lucsch/ESP32Marauder/esp32_marauder_pio/data/marauder3L1.jpg

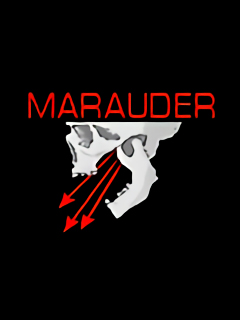
esp32_marauder_pio/data/marauder3L1.jpg
