lucsch/ESP32Marauder/esp32_marauder_pio/data/marauder_mini.jpg

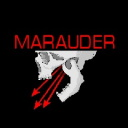
esp32_marauder_pio/data/marauder_mini.jpg
