lucsch/ESP32Marauder/pictures/jcmk_square_sticker_500px.png

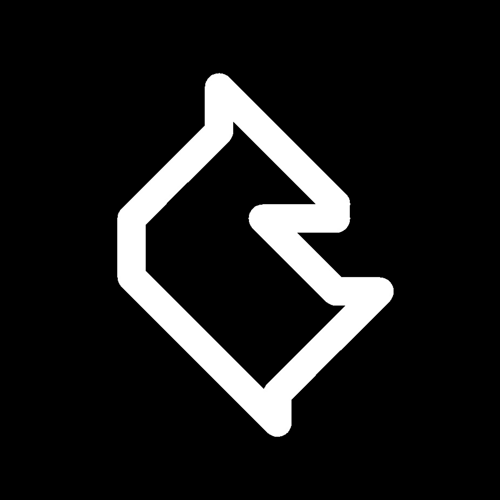
pictures/jcmk_square_sticker_500px.png
