lucsch/ESP32Marauder/mechanical/V7/Battery Cover.stl

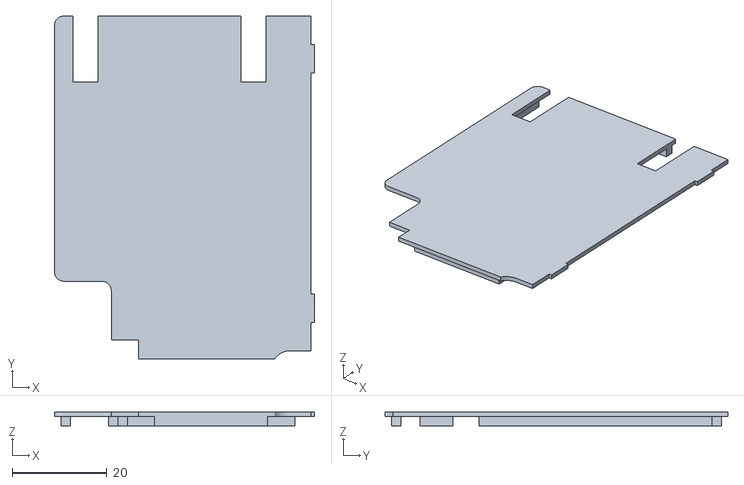
[picture p25: CAD file, 2025-01-28]
mechanical/V7/Battery Cover.stl
54.9 x 72.4 x 3.00
