lucsch/ESP32Marauder/mechanical/V7/Power Switch.stl

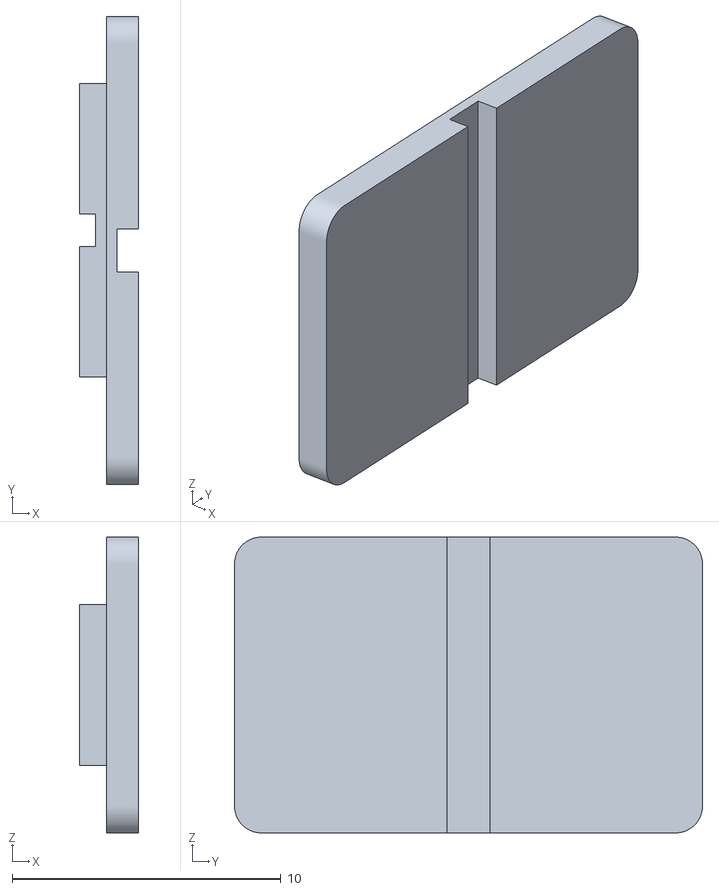
[picture p27: CAD file, 2025-01-28]
mechanical/V7/Power Switch.stl
2.20 x 17.4 x 11.0
