lucsch/ESP32Marauder/mechanical/C5 Adapter/Extra designs/c5 adapter back - hatched 1.stl

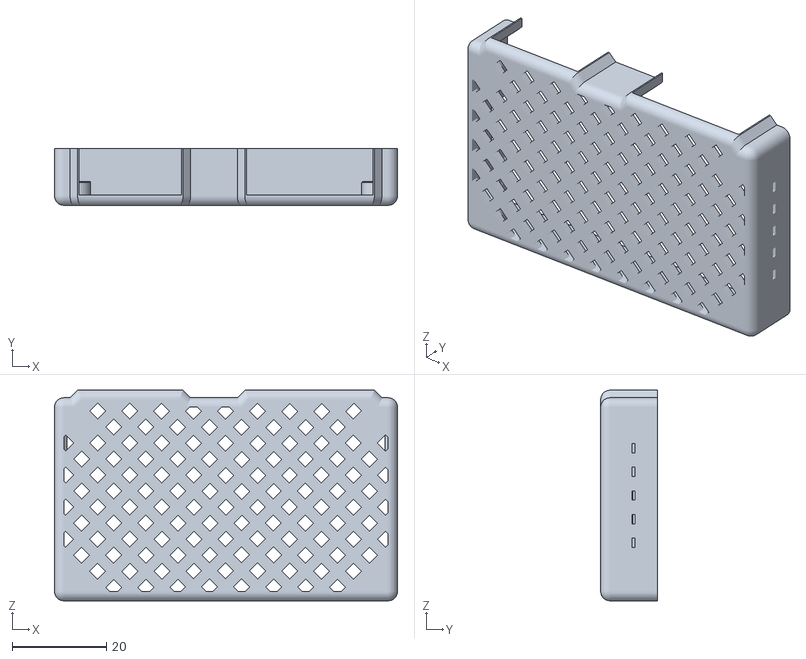
[picture p28: CAD file, 2025-09-12]
mechanical/C5 Adapter/Extra designs/c5 adapter back - hatched 1.stl
72.6 x 12.0 x 44.6
