lucsch/ESP32Marauder/pictures/BFFB NRF24 Fix/DSC05049-Edit.jpg

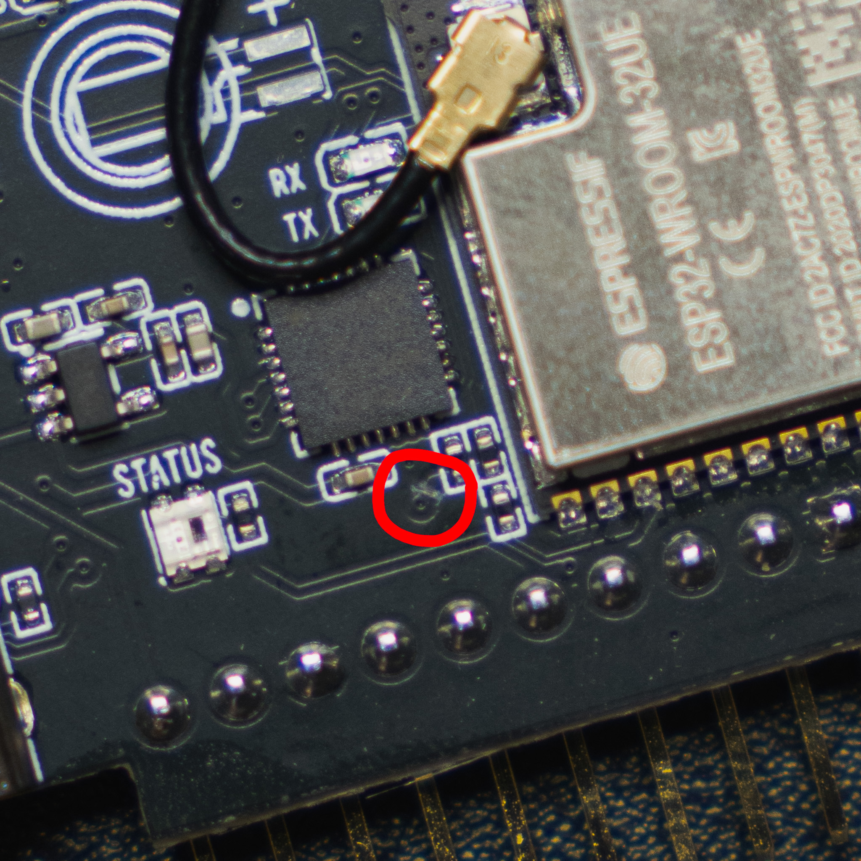
pictures/BFFB NRF24 Fix/DSC05049-Edit.jpg
