lucsch/ESP32Marauder/pictures/BFFB NRF24 Fix/DSC05050.jpg

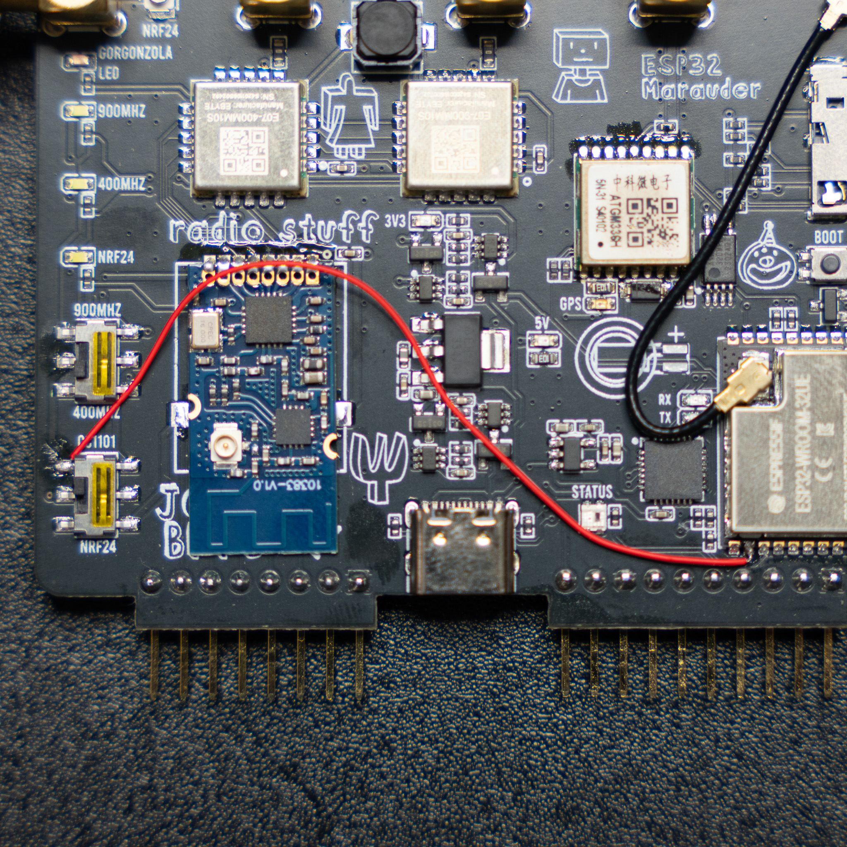
pictures/BFFB NRF24 Fix/DSC05050.jpg
