lucsch/ESP32Marauder/schematics/ch340/ch340_test.kicad_sch

## KiCad design schematics/ch340/ch340_test.kicad_sch (2024-10-28)

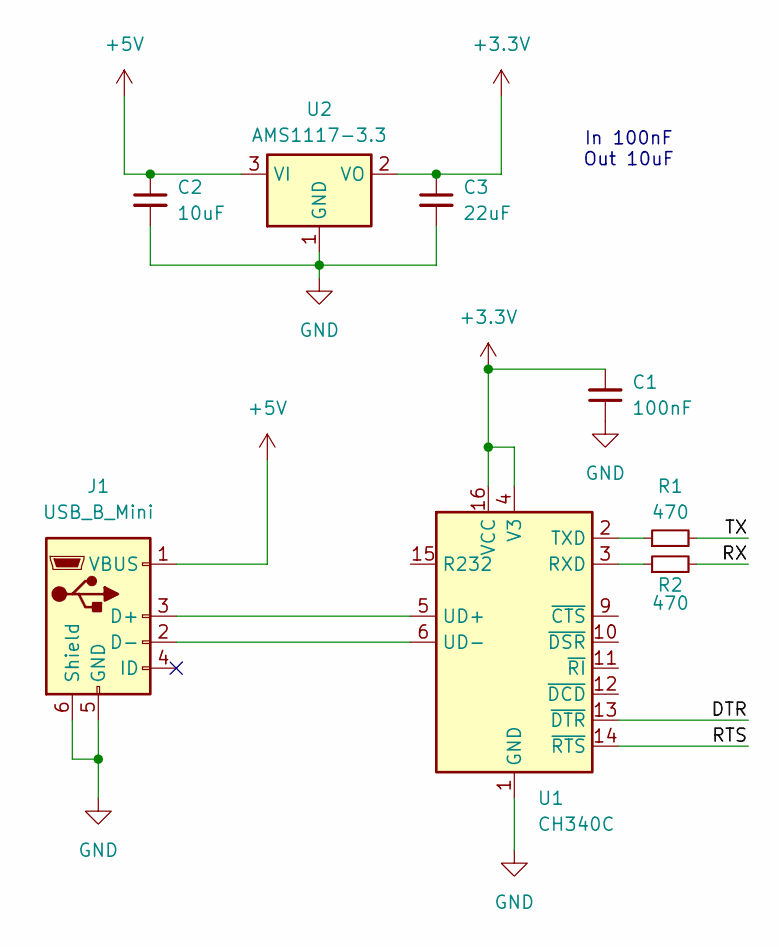
[picture p31: schematic ch340_test.kicad_sch]

Parts:
C1: 100nF
C2: 10uF
C3: 22uF
J1: USB_B_Mini
R1, R2: 470
U1: CH340C; SOIC-16_3.9x9.9mm_P1.27mm
U2: AMS1117-3.3; SOT-223-3_TabPin2

Connections:
+3.3V: C1.2, C3.1, U1.4 (V3), U1.16 (VCC), U2.2 (VO)
+5V: C2.1, J1.1 (VBUS), U2.3 (VI)
DTR: U1.13 (~DTR)
GND: C1.1, C2.2, C3.2, J1.5 (GND), J1.6 (Shield), U1.1 (GND), U2.1 (GND)
unnamed: J1.2 (D-), U1.6 (UD-)
unnamed: J1.3 (D+), U1.5 (UD+)
unnamed: R1.1, U1.2 (TXD)
unnamed: R2.1, U1.3 (RXD)
RTS: U1.14 (~RTS)
RX: R2.2
TX: R1.2

Notes on the sheet:
In 100nF Out 10uF
