lucsch/ESP32Marauder/esp32_marauder/MenuFunctions.cpp

#include "MenuFunctions.h"
#include "lang_var.h"
//#include "icons.h"

#ifdef HAS_SCREEN

extern const unsigned char menu_icons[][66];
PROGMEM lv_obj_t * slider_label;
PROGMEM lv_obj_t * ta1;
PROGMEM lv_obj_t * ta2;
PROGMEM lv_obj_t * save_name;

MenuFunctions::MenuFunctions()
{
}

// LVGL Stuff
/* Interrupt driven periodic handler */

#ifdef HAS_ILI9341
  void MenuFunctions::lv_tick_handler()
  {
    lv_tick_inc(LVGL_TICK_PERIOD);
  }
  
  /* Display flushing */
  void my_disp_flush(lv_disp_drv_t *disp, const lv_area_t *area, lv_color_t *color_p)
  {
    extern Display display_obj;
    uint16_t c;
  
    display_obj.tft.startWrite();
    display_obj.tft.setAddrWindow(area->x1, area->y1, (area->x2 - area->x1 + 1), (area->y2 - area->y1 + 1));
    for (int y = area->y1; y <= area->y2; y++) {
      for (int x = area->x1; x <= area->x2; x++) {
        c = color_p->full;
        display_obj.tft.writeColor(c, 1);
        color_p++;
      }
    }
    display_obj.tft.endWrite();
    lv_disp_flush_ready(disp);
  }
  
  
  bool my_touchpad_read(lv_indev_drv_t * indev_driver, lv_indev_data_t * data)
  {
    extern Display display_obj;
    
    uint16_t touchX, touchY;
  
    bool touched = display_obj.updateTouch(&touchX, &touchY, 600);
  
    if(!touched)
    {
      return false;
    }
  
    if(touchX>WIDTH_1 || touchY > HEIGHT_1)
    {
      Serial.println("Y or y outside of expected parameters..");
      Serial.print("y:");
      Serial.print(touchX);
      Serial.print(" x:");
      Serial.print(touchY);
    }
    else
    {
  
      data->state = touched ? LV_INDEV_STATE_PR : LV_INDEV_STATE_REL; 
       
      data->point.x = touchX;
      data->point.y = touchY;
  
    }
  
    return false;
  }
  
  void MenuFunctions::initLVGL() {
    tick.attach_ms(LVGL_TICK_PERIOD, lv_tick_handler);
    
    lv_init();
  
    lv_disp_buf_init(&disp_buf, buf, NULL, LV_HOR_RES_MAX * 10);
  
    lv_disp_drv_t disp_drv;
    lv_disp_drv_init(&disp_drv);
    disp_drv.hor_res = WIDTH_1;
    disp_drv.ver_res = HEIGHT_1;
    disp_drv.flush_cb = my_disp_flush;
    disp_drv.buffer = &disp_buf;
    lv_disp_drv_register(&disp_drv);
  
    lv_indev_drv_t indev_drv;
    lv_indev_drv_init(&indev_drv);             
    indev_drv.type = LV_INDEV_TYPE_POINTER;    
    indev_drv.read_cb = my_touchpad_read;      
    lv_indev_drv_register(&indev_drv);         
  }
  
  
  void MenuFunctions::deinitLVGL() {
    Serial.println(F("Deinit LVGL"));
    //lv_deinit();
  }
  
  
  // Event handler for settings drop down menus
  void setting_dropdown_cb(lv_obj_t * obj, lv_event_t event) {

  }

  // GFX Function to build a list showing all Stations scanned
  void MenuFunctions::addStationGFX(){
    extern LinkedList<Station>* stations;
    extern LinkedList<AccessPoint>* access_points;
    extern WiFiScan wifi_scan_obj;
  
    lv_obj_t * list1 = lv_list_create(lv_scr_act(), NULL);
    lv_obj_set_size(list1, 160, 200);
    lv_obj_set_width(list1, LV_HOR_RES);
    lv_obj_align(list1, NULL, LV_ALIGN_CENTER, 0, 0);
  
    lv_obj_t * list_btn;
  
    lv_obj_t * label;
  
    list_btn = lv_list_add_btn(list1, LV_SYMBOL_CLOSE, text09);
    lv_obj_set_event_cb(list_btn, station_list_cb);

    char addr[] = "00:00:00:00:00:00";
    for (int x = 0; x < access_points->size(); x++) {
      AccessPoint cur_ap = access_points->get(x);

      // Add non clickable button for AP
      String full_label = "AP: " + cur_ap.essid;
      char buf[full_label.length() + 1] = {};
      full_label.toCharArray(buf, full_label.length() + 1);
      list_btn = lv_list_add_btn(list1, NULL, buf);
      lv_btn_set_checkable(list_btn, false);
      
      int cur_ap_sta_len = access_points->get(x).stations->size();
      for (int y = 0; y < cur_ap_sta_len; y++) {
        Station cur_sta = stations->get(cur_ap.stations->get(y));
        // Convert uint8_t MAC to char array
        wifi_scan_obj.getMAC(addr, cur_sta.mac, 0);
        
        list_btn = lv_list_add_btn(list1, LV_SYMBOL_WIFI, addr);
        lv_btn_set_checkable(list_btn, true);
        lv_obj_set_event_cb(list_btn, station_list_cb);
    
        if (cur_sta.selected)
          lv_btn_toggle(list_btn);
      }
    }
  }

  // Function to work with list of Stations
  void station_list_cb(lv_obj_t * btn, lv_event_t event) {
    extern LinkedList<Station>* stations;
    extern MenuFunctions menu_function_obj;
    extern WiFiScan wifi_scan_obj;
  
    String btn_text = lv_list_get_btn_text(btn);
    String display_string = "";
    char addr[] = "00:00:00:00:00:00";
    
    if (event == LV_EVENT_CLICKED) {
      if (btn_text != text09) {
      }
      else {
        Serial.println("Exiting...");
        lv_obj_del_async(lv_obj_get_parent(lv_obj_get_parent(btn)));
  
        for (int i = 0; i < stations->size(); i++) {
          if (stations->get(i).selected) {
            wifi_scan_obj.getMAC(addr, stations->get(i).mac, 0);
            Serial.print("Selected: ");
            Serial.println(addr);
          }
        }
  
        printf("LV_EVENT_CANCEL\n");
        menu_function_obj.deinitLVGL();
        wifi_scan_obj.StartScan(WIFI_SCAN_OFF);
        display_obj.exit_draw = true; // set everything back to normal
      }
    }
    
    if (event == LV_EVENT_VALUE_CHANGED) {     
      if (lv_btn_get_state(btn) == LV_BTN_STATE_CHECKED_RELEASED) {
        for (int i = 0; i < stations->size(); i++) {
          wifi_scan_obj.getMAC(addr, stations->get(i).mac, 0); 
          if (strcmp(addr, btn_text.c_str()) == 0) {
            Serial.print("Adding Station: ");
            Serial.println(addr);
            Station sta = stations->get(i);
            sta.selected = true;
            stations->set(i, sta);
          }
        }
      }
      else {
        for (int i = 0; i < stations->size(); i++) {
          wifi_scan_obj.getMAC(addr, stations->get(i).mac, 0); 
          if (strcmp(addr, btn_text.c_str()) == 0) {
            Serial.print("Removing Station: ");
            Serial.println(addr);
            Station sta = stations->get(i);
            sta.selected = false;
            stations->set(i, sta);
          }
        }
      }
    }
  }

  // GFX Function to build a list showing all EP HTML Files
  void MenuFunctions::selectEPHTMLGFX() {
    extern EvilPortal evil_portal_obj;
  
    lv_obj_t * list1 = lv_list_create(lv_scr_act(), NULL);
    lv_obj_set_size(list1, 160, 200);
    lv_obj_set_width(list1, LV_HOR_RES);
    lv_obj_align(list1, NULL, LV_ALIGN_CENTER, 0, 0);
  
    lv_obj_t * list_btn;
  
    lv_obj_t * label;
  
    list_btn = lv_list_add_btn(list1, LV_SYMBOL_CLOSE, text09);
    lv_obj_set_event_cb(list_btn, html_list_cb);
  
    for (int i = 1; i < evil_portal_obj.html_files->size(); i++) {
      char buf[evil_portal_obj.html_files->get(i).length() + 1] = {};
      evil_portal_obj.html_files->get(i).toCharArray(buf, evil_portal_obj.html_files->get(i).length() + 1);
      
      list_btn = lv_list_add_btn(list1, LV_SYMBOL_FILE, buf);
      lv_btn_set_checkable(list_btn, true);
      lv_obj_set_event_cb(list_btn, html_list_cb);
  
      if (i == evil_portal_obj.selected_html_index)
        lv_btn_toggle(list_btn);
    }
  }

  void html_list_cb(lv_obj_t * btn, lv_event_t event) {
    extern EvilPortal evil_portal_obj;
    extern MenuFunctions menu_function_obj;
  
    String btn_text = lv_list_get_btn_text(btn);
    String display_string = "";
    
    if (event == LV_EVENT_CLICKED) {
      if (btn_text != text09) {
      }
      else {
        Serial.println("Exiting...");
        lv_obj_del_async(lv_obj_get_parent(lv_obj_get_parent(btn)));
  
        for (int i = 1; i < evil_portal_obj.html_files->size(); i++) {
          if (i == evil_portal_obj.selected_html_index) {
            Serial.println("Selected: " + (String)evil_portal_obj.html_files->get(i));
          }
        }
  
        printf("LV_EVENT_CANCEL\n");
        menu_function_obj.deinitLVGL();
        wifi_scan_obj.StartScan(WIFI_SCAN_OFF);
        display_obj.exit_draw = true; // set everything back to normal
      }
    }
    
    if (event == LV_EVENT_VALUE_CHANGED) {      
      if (lv_btn_get_state(btn) == LV_BTN_STATE_CHECKED_RELEASED) {
        for (int i = 1; i < evil_portal_obj.html_files->size(); i++) {
          if (evil_portal_obj.html_files->get(i) == btn_text) {
            Serial.println("Setting HTML: " + (String)evil_portal_obj.html_files->get(i));
            evil_portal_obj.selected_html_index = i;
            evil_portal_obj.target_html_name = (String)evil_portal_obj.html_files->get(i);
          }
        }

        // Deselect buttons that were previously selected
        lv_obj_t * list = lv_obj_get_parent(btn);

        lv_obj_t * next_btn = lv_obj_get_child(list, NULL);
        while (next_btn != NULL) {
          if (next_btn != btn) {
            lv_btn_set_state(next_btn, LV_BTN_STATE_RELEASED);
          }
          next_btn = lv_obj_get_child(list, next_btn);
        }
      }
    }
  }
  
  // GFX Function to build a list showing all APs scanned
  void MenuFunctions::addAPGFX(String type){
    extern WiFiScan wifi_scan_obj;
    extern LinkedList<AccessPoint>* access_points;
    extern LinkedList<AirTag>* airtags;
  
    lv_obj_t * list1 = lv_list_create(lv_scr_act(), NULL);
    lv_obj_set_size(list1, 160, 200);
    lv_obj_set_width(list1, LV_HOR_RES);
    lv_obj_align(list1, NULL, LV_ALIGN_CENTER, 0, 0);
  
    lv_obj_t * list_btn;
  
    lv_obj_t * label;
  
    list_btn = lv_list_add_btn(list1, LV_SYMBOL_CLOSE, text09);
    lv_obj_set_event_cb(list_btn, ap_list_cb);
  
    if ((type == "AP") || (type == "AP Info")) {
      for (int i = 0; i < access_points->size(); i++) {
        char buf[access_points->get(i).essid.length() + 1] = {};
        access_points->get(i).essid.toCharArray(buf, access_points->get(i).essid.length() + 1);
        
        list_btn = lv_list_add_btn(list1, LV_SYMBOL_WIFI, buf);
        lv_btn_set_checkable(list_btn, true);
        if (type == "AP")
          lv_obj_set_event_cb(list_btn, ap_list_cb);
        else if (type == "AP Info")
          lv_obj_set_event_cb(list_btn, ap_info_list_cb);
    
        if (access_points->get(i).selected)
          lv_btn_toggle(list_btn);
      }
    }
    else if (type == "Airtag") {
      for (int i = 0; i < airtags->size(); i++) {
        char buf[airtags->get(i).mac.length() + 1] = {};
        airtags->get(i).mac.toCharArray(buf, airtags->get(i).mac.length() + 1);
        
        list_btn = lv_list_add_btn(list1, LV_SYMBOL_BLUETOOTH, buf);
        lv_btn_set_checkable(list_btn, true);
        lv_obj_set_event_cb(list_btn, at_list_cb);
    
        //if (airtags->get(i).selected)
        //  lv_btn_toggle(list_btn);
      }
    }
  }
  
  void at_list_cb(lv_obj_t * btn, lv_event_t event) {
    extern MenuFunctions menu_function_obj;
    extern WiFiScan wifi_scan_obj;
    extern LinkedList<AirTag>* airtags;
    extern Display display_obj;
  
    String btn_text = lv_list_get_btn_text(btn);
    String display_string = "";
    
    // Button is clicked
    if (event == LV_EVENT_CLICKED) {
      if (btn_text != text09) {
      }
      // It's the back button
      else {
        Serial.println("Exiting...");
        lv_obj_del_async(lv_obj_get_parent(lv_obj_get_parent(btn)));
  
        for (int i = 0; i < airtags->size(); i++) {
          if (airtags->get(i).selected) {
            Serial.println("Selected: " + (String)airtags->get(i).mac);
          }
        }
  
        printf("LV_EVENT_CANCEL\n");
        menu_function_obj.deinitLVGL();
        wifi_scan_obj.StartScan(WIFI_SCAN_OFF);
        display_obj.exit_draw = true; // set everything back to normal
      }
    }
    
    if (event == LV_EVENT_VALUE_CHANGED) {      
      if (lv_btn_get_state(btn) == LV_BTN_STATE_CHECKED_RELEASED) {
        bool do_that_thang = false;
        for (int i = 0; i < airtags->size(); i++) {
          if (airtags->get(i).mac == btn_text) {
            Serial.println("Selecting Airtag: " + (String)airtags->get(i).mac);
            AirTag at = airtags->get(i);
            at.selected = true;
            airtags->set(i, at);
            do_that_thang = true;
          }
          else {
            AirTag at = airtags->get(i);
            at.selected = false;
            airtags->set(i, at);
          }
        }
        // Start spoofing airtag
        if (do_that_thang) {
          menu_function_obj.deinitLVGL();
          lv_obj_del_async(lv_obj_get_parent(lv_obj_get_parent(btn)));
          wifi_scan_obj.StartScan(WIFI_SCAN_OFF);
          display_obj.clearScreen();
          menu_function_obj.orientDisplay();
          display_obj.clearScreen();
          menu_function_obj.drawStatusBar();
          wifi_scan_obj.StartScan(BT_SPOOF_AIRTAG, TFT_WHITE);
        }
      }
      else {
        for (int i = 0; i < airtags->size(); i++) {
          if (airtags->get(i).mac == btn_text) {
            Serial.println("Deselecting Airtag: " + (String)airtags->get(i).mac);
            AirTag at = airtags->get(i);
            at.selected = false;
            airtags->set(i, at);
          }
        }
      }
    }
  }
  
  void ap_list_cb(lv_obj_t * btn, lv_event_t event) {
    extern LinkedList<AccessPoint>* access_points;
    extern MenuFunctions menu_function_obj;
    extern WiFiScan wifi_scan_obj;
  
    String btn_text = lv_list_get_btn_text(btn);
    String display_string = "";
    
    if (event == LV_EVENT_CLICKED) {
      if (btn_text != text09) {
      }
      else {
        Serial.println("Exiting...");
        lv_obj_del_async(lv_obj_get_parent(lv_obj_get_parent(btn)));
  
        for (int i = 0; i < access_points->size(); i++) {
          if (access_points->get(i).selected) {
            Serial.println("Selected: " + (String)access_points->get(i).essid);
          }
        }
  
        printf("LV_EVENT_CANCEL\n");
        menu_function_obj.deinitLVGL();
        wifi_scan_obj.StartScan(WIFI_SCAN_OFF);
        display_obj.exit_draw = true; // set everything back to normal
      }
    }
    
    if (event == LV_EVENT_VALUE_CHANGED) {      
      if (lv_btn_get_state(btn) == LV_BTN_STATE_CHECKED_RELEASED) {
        for (int i = 0; i < access_points->size(); i++) {
          if (access_points->get(i).essid == btn_text) {
            Serial.println("Adding AP: " + (String)access_points->get(i).essid);
            AccessPoint ap = access_points->get(i);
            ap.selected = true;
            access_points->set(i, ap);
          }
        }
      }
      else {
        for (int i = 0; i < access_points->size(); i++) {
          if (access_points->get(i).essid == btn_text) {
            Serial.println("Removing AP: " + (String)access_points->get(i).essid);
            AccessPoint ap = access_points->get(i);
            ap.selected = false;
            access_points->set(i, ap);
          }
        }
      }
    }
  }

  void ap_info_list_cb(lv_obj_t * btn, lv_event_t event) {
    extern LinkedList<AccessPoint>* access_points;
    extern MenuFunctions menu_function_obj;
    extern WiFiScan wifi_scan_obj;
  
    String btn_text = lv_list_get_btn_text(btn);
    String display_string = "";
    
    // Exit function
    if (event == LV_EVENT_CLICKED) {
      if (btn_text != text09) {
        for (int i = 0; i < access_points->size(); i++) {
          if (access_points->get(i).essid == btn_text) {
            lv_obj_del_async(lv_obj_get_parent(lv_obj_get_parent(btn)));
  
            printf("LV_EVENT_CANCEL\n");
            menu_function_obj.deinitLVGL();
            wifi_scan_obj.StartScan(WIFI_SCAN_OFF);
            //display_obj.exit_draw = true; // set everything back to normal
            menu_function_obj.orientDisplay();
            menu_function_obj.changeMenu(&menu_function_obj.apInfoMenu);
            wifi_scan_obj.RunAPInfo(i);
          }
        }
      }
      else {
        Serial.println("Exiting...");
        lv_obj_del_async(lv_obj_get_parent(lv_obj_get_parent(btn)));
  
        printf("LV_EVENT_CANCEL\n");
        menu_function_obj.deinitLVGL();
        wifi_scan_obj.StartScan(WIFI_SCAN_OFF);
        display_obj.exit_draw = true; // set everything back to normal
      }
    }
  }
  
  void MenuFunctions::addSSIDGFX(){
    extern LinkedList<ssid>* ssids;
    
    String display_string = "";
    // Create a keyboard and apply the styles
    kb = lv_keyboard_create(lv_scr_act(), NULL);
    lv_obj_set_size(kb, LV_HOR_RES, LV_VER_RES / 2);
    lv_obj_set_event_cb(kb, add_ssid_keyboard_event_cb);
  
    // Create one text area
    // Store all SSIDs
    ta1 = lv_textarea_create(lv_scr_act(), NULL);
    lv_textarea_set_one_line(ta1, false);
    lv_obj_set_width(ta1, LV_HOR_RES);
    lv_obj_set_height(ta1, (LV_VER_RES / 2) - 35);
    lv_obj_set_pos(ta1, 5, 20);
    lv_textarea_set_cursor_hidden(ta1, true);
    lv_obj_align(ta1, NULL, LV_ALIGN_IN_TOP_MID, NULL, NULL);
    lv_textarea_set_placeholder_text(ta1, text_table1[0]);
  
    // Create second text area
    // Add SSIDs
    ta2 = lv_textarea_create(lv_scr_act(), ta1);
    lv_textarea_set_cursor_hidden(ta2, false);
    lv_textarea_set_one_line(ta2, true);
    lv_obj_align(ta2, NULL, LV_ALIGN_IN_TOP_MID, NULL, (LV_VER_RES / 2) - 35);
    lv_textarea_set_text(ta2, "");
    lv_textarea_set_placeholder_text(ta2, text_table1[1]);
  
    // After generating text areas, add text to first text box
    for (int i = 0; i < ssids->size(); i++)
      display_string.concat((String)ssids->get(i).essid + "\n");
      
    lv_textarea_set_text(ta1, display_string.c_str());
  
    // Focus it on one of the text areas to start
    lv_keyboard_set_textarea(kb, ta2);
    lv_keyboard_set_cursor_manage(kb, true);
    
  }
  
  // Keyboard callback dedicated to joining wifi
  void add_ssid_keyboard_event_cb(lv_obj_t * keyboard, lv_event_t event){
    extern Display display_obj;
    extern MenuFunctions menu_function_obj;
    extern WiFiScan wifi_scan_obj;
    extern LinkedList<ssid>* ssids;
    
    lv_keyboard_def_event_cb(kb, event);
  
    // User has applied text box
    if(event == LV_EVENT_APPLY){
      String display_string = "";
      printf("LV_EVENT_APPLY\n");
  
      // Get text from SSID text box
      String ta2_text = lv_textarea_get_text(ta2);
      Serial.println(ta2_text);
  
      // Add text box text to list of SSIDs
      wifi_scan_obj.addSSID(ta2_text);
  
      // Update large text box with ssid
      for (int i = 0; i < ssids->size(); i++)
        display_string.concat((String)ssids->get(i).essid + "\n");
      lv_textarea_set_text(ta1, display_string.c_str());
  
      lv_textarea_set_text(ta2, "");
    }else if(event == LV_EVENT_CANCEL){
      printf("LV_EVENT_CANCEL\n");
      menu_function_obj.deinitLVGL();
      display_obj.exit_draw = true; // set everything back to normal
    }
  }

  void MenuFunctions::joinWiFiGFX(String essid){

    // Create one text area
    ta1 = lv_textarea_create(lv_scr_act(), NULL);
    lv_textarea_set_one_line(ta1, true);
    lv_obj_set_width(ta1, LV_HOR_RES / 2 - 20);
    lv_obj_set_pos(ta1, 5, 20);
    //lv_ta_set_cursor_type(ta, LV_CURSOR_BLOCK);
    lv_textarea_set_text(ta1, essid.c_str());
    lv_obj_set_event_cb(ta1, ta_event_cb);

    // Create first label
    lv_obj_t * ssid_label = lv_label_create(lv_scr_act(), NULL);
    lv_label_set_text(ssid_label, "SSID:");
    lv_obj_align(ssid_label, ta1, LV_ALIGN_OUT_TOP_LEFT, 0, 0);

    // Create second text area
    ta2 = lv_textarea_create(lv_scr_act(), ta1);
    //lv_textarea_set_pwd_mode(ta2, true); // This shit makes it so backspace does not work
    //lv_textarea_set_pwd_show_time(ta2, 1000);
    lv_textarea_set_cursor_hidden(ta2, true);
    lv_obj_align(ta2, NULL, LV_ALIGN_IN_TOP_RIGHT, -5, 20);

    // Create second label
    lv_obj_t * pw_label = lv_label_create(lv_scr_act(), NULL);
    lv_label_set_text(pw_label, "Password:");
    lv_textarea_set_text(ta2, "");
    lv_obj_align(pw_label, ta2, LV_ALIGN_OUT_TOP_LEFT, 0, 0);

    // Create a keyboard and apply the styles
    kb = lv_keyboard_create(lv_scr_act(), NULL);
    lv_obj_set_size(kb, LV_HOR_RES, LV_VER_RES / 2);
    lv_obj_set_event_cb(kb, join_wifi_keyboard_event_cb);

    // Focus it on one of the text areas to start
    lv_keyboard_set_textarea(kb, ta1);
    lv_keyboard_set_cursor_manage(kb, true);
    
  }

  void join_wifi_keyboard_event_cb(lv_obj_t * keyboard, lv_event_t event){
    extern Display display_obj;
    extern MenuFunctions menu_function_obj;
    extern WiFiScan wifi_scan_obj;
    lv_keyboard_def_event_cb(kb, event);
    if(event == LV_EVENT_APPLY){
      printf("LV_EVENT_APPLY\n");
      //String ta1_text = lv_textarea_get_text(lv_keyboard_get_textarea(kb));
      String ta1_text = lv_textarea_get_text(ta1);
      String ta2_text = lv_textarea_get_text(ta2);
      Serial.println(ta1_text);
      Serial.println(ta2_text);
      if (wifi_scan_obj.joinWiFi(ta1_text, ta2_text))
        wifi_scan_obj.currentScanMode = WIFI_CONNECTED;
      else
        wifi_scan_obj.currentScanMode = WIFI_SCAN_OFF;
    }else if(event == LV_EVENT_CANCEL){
      printf("LV_EVENT_CANCEL\n");
      //lv_textarea_set_text(lv_keyboard_get_textarea(kb), "");
      menu_function_obj.deinitLVGL();
      //wifi_scan_obj.StartScan(WIFI_SCAN_OFF);
      display_obj.exit_draw = true; // set everything back to normal
      if (wifi_scan_obj.connected_network != "")
        wifi_scan_obj.currentScanMode = WIFI_CONNECTED;
    }
  }
  
  
  void ta_event_cb(lv_obj_t * ta, lv_event_t event)
  {
    if(event == LV_EVENT_CLICKED) {
      if(kb != NULL)
        lv_keyboard_set_textarea(kb, ta);
    }
  
  }

#endif
//// END LV_ARDUINO STUFF

void MenuFunctions::buttonNotSelected(int b, int x) {
  if (x == -1)
    x = b;

  // Ensure b is within valid button index range
  b = (x - menu_start_index) % BUTTON_SCREEN_LIMIT;

  #ifdef HAS_MINI_SCREEN
    display_obj.tft.setFreeFont(NULL);
    display_obj.key[b].drawButton(false, current_menu->list->get(x).name);
  #endif

  uint16_t color = this->getColor(current_menu->list->get(x).color);

  #ifdef HAS_FULL_SCREEN
    display_obj.tft.setFreeFont(MENU_FONT);
    display_obj.key[b].drawButton(false, current_menu->list->get(x).name);
    if ((current_menu->list->get(x).name != text09) && (current_menu->list->get(x).icon != 255))
          display_obj.tft.drawXBitmap(0,
                                      KEY_Y + (b * (KEY_H + KEY_SPACING_Y)) - (ICON_H / 2),
                                      menu_icons[current_menu->list->get(x).icon],
                                      ICON_W,
                                      ICON_H,
                                      TFT_BLACK,
                                      color);
    display_obj.tft.setFreeFont(NULL);
  #endif
}

void MenuFunctions::buttonSelected(int b, int x) {
  if (x == -1)
    x = b;

  // Ensure b is within valid button index range
  b = (x - menu_start_index) % BUTTON_SCREEN_LIMIT;

  uint16_t color = this->getColor(current_menu->list->get(x).color);

  #ifdef HAS_MINI_SCREEN
    display_obj.tft.setFreeFont(NULL);
    display_obj.key[b].drawButton(true, current_menu->list->get(x).name);
  #endif

  #ifdef HAS_FULL_SCREEN
    display_obj.tft.setFreeFont(MENU_FONT);
    display_obj.key[b].drawButton(true, current_menu->list->get(x).name);
    if ((current_menu->list->get(x).name != text09) && (current_menu->list->get(x).icon != 255))
          display_obj.tft.drawXBitmap(0,
                                      KEY_Y + (b * (KEY_H + KEY_SPACING_Y)) - (ICON_H / 2),
                                      menu_icons[current_menu->list->get(x).icon],
                                      ICON_W,
                                      ICON_H,
                                      TFT_BLACK,
                                      color);
    display_obj.tft.setFreeFont(NULL);
  #endif
}

void MenuFunctions::displayMenuButtons() {
  #ifdef HAS_ILI9341
    // Draw lines to show each menu button
    for (int i = 0; i < 3; i++) {

      // Draw horizontal line on left
      display_obj.tft.drawLine(0, 
                              TFT_HEIGHT / 3 * (i),
                              (TFT_WIDTH / 12) / 2,
                              TFT_HEIGHT / 3 * (i),
                              TFT_FARTGRAY);

      // Draw horizontal line on right
      display_obj.tft.drawLine(TFT_WIDTH - 1 - ((TFT_WIDTH / 12) / 2), 
                              TFT_HEIGHT / 3 * (i),
                              TFT_WIDTH,
                              TFT_HEIGHT / 3 * (i),
                              TFT_FARTGRAY);

      // Draw vertical line on left
      display_obj.tft.drawLine(0, 
                              (TFT_HEIGHT / 3 * (i)) - ((TFT_WIDTH / 12) / 2),
                              0,
                              (TFT_HEIGHT / 3 * (i)) + ((TFT_WIDTH / 12) / 2),
                              TFT_FARTGRAY);

      // Draw vertical line on right
      display_obj.tft.drawLine(TFT_WIDTH - 1, 
                              (TFT_HEIGHT / 3 * (i)) - ((TFT_WIDTH / 12) / 2),
                              TFT_WIDTH - 1,
                              (TFT_HEIGHT / 3 * (i)) + ((TFT_WIDTH / 12) / 2),
                              TFT_FARTGRAY);
    }
  #endif
}

// Function to check menu input
void MenuFunctions::main(uint32_t currentTime)
{
  // Some function exited and we need to go back to normal
  if (display_obj.exit_draw) {
    if (wifi_scan_obj.currentScanMode != WIFI_CONNECTED)
      wifi_scan_obj.currentScanMode = WIFI_SCAN_OFF;
    display_obj.exit_draw = false;
    this->orientDisplay();
  }
  if ((wifi_scan_obj.currentScanMode == WIFI_SCAN_OFF) ||
      (wifi_scan_obj.currentScanMode == WIFI_CONNECTED) ||
      (wifi_scan_obj.currentScanMode == OTA_UPDATE) ||
      (wifi_scan_obj.currentScanMode == ESP_UPDATE) ||
      (wifi_scan_obj.currentScanMode == SHOW_INFO) ||
      (wifi_scan_obj.currentScanMode == WIFI_SCAN_GPS_DATA) ||
      (wifi_scan_obj.currentScanMode == GPS_POI) ||
      (wifi_scan_obj.currentScanMode == GPS_TRACKER) ||
      (wifi_scan_obj.currentScanMode == WIFI_SCAN_GPS_NMEA)) {
    if (wifi_scan_obj.orient_display) {
      this->orientDisplay();
      wifi_scan_obj.orient_display = false;
    }
  }

  if (currentTime != 0) {
    if (currentTime - initTime >= BANNER_TIME) {
      this->initTime = millis();
      if ((wifi_scan_obj.currentScanMode != LV_JOIN_WIFI) &&
          (wifi_scan_obj.currentScanMode != LV_ADD_SSID))
        this->updateStatusBar();
      
      // Do channel analyzer stuff
      if ((wifi_scan_obj.currentScanMode == WIFI_SCAN_CHAN_ANALYZER) ||
          (wifi_scan_obj.currentScanMode == BT_SCAN_ANALYZER)){
        #ifdef HAS_SCREEN
          this->setGraphScale(this->graphScaleCheck(wifi_scan_obj._analyzer_values));

          this->drawGraph(wifi_scan_obj._analyzer_values);
        #endif
      }
    }
  }


  boolean pressed = false;
  // This is code from bodmer's keypad example
  uint16_t t_x = 0, t_y = 0; // To store the touch coordinates

  // Get the display buffer out of the way
  if ((wifi_scan_obj.currentScanMode != WIFI_SCAN_OFF ) &&
      (wifi_scan_obj.currentScanMode != WIFI_CONNECTED) &&
      (wifi_scan_obj.currentScanMode != WIFI_ATTACK_BEACON_SPAM) &&
      (wifi_scan_obj.currentScanMode != WIFI_ATTACK_AP_SPAM) &&
      (wifi_scan_obj.currentScanMode != WIFI_ATTACK_AUTH) &&
      (wifi_scan_obj.currentScanMode != WIFI_ATTACK_DEAUTH) &&
      (wifi_scan_obj.currentScanMode != WIFI_ATTACK_DEAUTH_MANUAL) &&
      (wifi_scan_obj.currentScanMode != WIFI_ATTACK_DEAUTH_TARGETED) &&
      (wifi_scan_obj.currentScanMode != WIFI_ATTACK_BAD_MSG_TARGETED) &&
      (wifi_scan_obj.currentScanMode != WIFI_ATTACK_BAD_MSG) &&
      (wifi_scan_obj.currentScanMode != WIFI_ATTACK_SLEEP) &&
      (wifi_scan_obj.currentScanMode != WIFI_ATTACK_SLEEP_TARGETED) &&
      (wifi_scan_obj.currentScanMode != WIFI_ATTACK_MIMIC) &&
      (wifi_scan_obj.currentScanMode != WIFI_ATTACK_RICK_ROLL))
    display_obj.displayBuffer();


  int pre_getTouch = millis();

  #ifdef HAS_ILI9341
    if (!this->disable_touch)
      pressed = display_obj.updateTouch(&t_x, &t_y);
  #endif


  // This is if there are scans/attacks going on
  #ifdef HAS_ILI9341
    if ((wifi_scan_obj.currentScanMode != WIFI_SCAN_OFF) &&
        (pressed) &&
        (wifi_scan_obj.currentScanMode != WIFI_CONNECTED) &&
        (wifi_scan_obj.currentScanMode != OTA_UPDATE) &&
        (wifi_scan_obj.currentScanMode != ESP_UPDATE) &&
        (wifi_scan_obj.currentScanMode != SHOW_INFO) &&
        (wifi_scan_obj.currentScanMode != WIFI_SCAN_GPS_DATA) &&
        (wifi_scan_obj.currentScanMode != GPS_POI) &&
        (wifi_scan_obj.currentScanMode != GPS_TRACKER) &&
        (wifi_scan_obj.currentScanMode != WIFI_SCAN_GPS_NMEA))
    {
      // Stop the current scan
      if ((wifi_scan_obj.currentScanMode == WIFI_SCAN_PROBE) ||
          (wifi_scan_obj.currentScanMode == WIFI_SCAN_STATION_WAR_DRIVE) ||
          (wifi_scan_obj.currentScanMode == WIFI_SCAN_STATION) ||
          (wifi_scan_obj.currentScanMode == WIFI_SCAN_AP) ||
          (wifi_scan_obj.currentScanMode == WIFI_SCAN_WAR_DRIVE) ||
          (wifi_scan_obj.currentScanMode == WIFI_SCAN_EVIL_PORTAL) ||
          (wifi_scan_obj.currentScanMode == WIFI_SCAN_TARGET_AP) ||
          (wifi_scan_obj.currentScanMode == WIFI_SCAN_TARGET_AP_FULL) ||
          (wifi_scan_obj.currentScanMode == WIFI_SCAN_AP_STA) ||
          (wifi_scan_obj.currentScanMode == WIFI_PING_SCAN) ||
          (wifi_scan_obj.currentScanMode == WIFI_ARP_SCAN) ||
          (wifi_scan_obj.currentScanMode == WIFI_PORT_SCAN_ALL) ||
          (wifi_scan_obj.currentScanMode == WIFI_SCAN_SSH) ||
          (wifi_scan_obj.currentScanMode == WIFI_SCAN_TELNET) ||
          (wifi_scan_obj.currentScanMode == WIFI_SCAN_PWN) ||
          (wifi_scan_obj.currentScanMode == WIFI_SCAN_PINESCAN) ||
          (wifi_scan_obj.currentScanMode == WIFI_SCAN_MULTISSID) ||
          (wifi_scan_obj.currentScanMode == WIFI_SCAN_ESPRESSIF) ||
          (wifi_scan_obj.currentScanMode == WIFI_SCAN_ALL) ||
          (wifi_scan_obj.currentScanMode == WIFI_SCAN_DEAUTH) ||
          (wifi_scan_obj.currentScanMode == WIFI_ATTACK_BEACON_SPAM) ||
          (wifi_scan_obj.currentScanMode == WIFI_ATTACK_AP_SPAM) ||
          (wifi_scan_obj.currentScanMode == WIFI_ATTACK_AUTH) ||
          (wifi_scan_obj.currentScanMode == WIFI_ATTACK_DEAUTH) ||
          (wifi_scan_obj.currentScanMode == WIFI_ATTACK_DEAUTH_MANUAL) ||
          (wifi_scan_obj.currentScanMode == WIFI_ATTACK_DEAUTH_TARGETED) ||
          (wifi_scan_obj.currentScanMode == WIFI_ATTACK_BAD_MSG_TARGETED) ||
          (wifi_scan_obj.currentScanMode == WIFI_ATTACK_BAD_MSG) ||
          (wifi_scan_obj.currentScanMode == WIFI_ATTACK_SLEEP) ||
          (wifi_scan_obj.currentScanMode == WIFI_ATTACK_SLEEP_TARGETED) ||
          (wifi_scan_obj.currentScanMode == WIFI_ATTACK_MIMIC) ||
          (wifi_scan_obj.currentScanMode == WIFI_ATTACK_RICK_ROLL) ||
          (wifi_scan_obj.currentScanMode == WIFI_ATTACK_BEACON_LIST) ||
          (wifi_scan_obj.currentScanMode == BT_SCAN_ALL) ||
          (wifi_scan_obj.currentScanMode == BT_SCAN_AIRTAG) ||
          (wifi_scan_obj.currentScanMode == BT_SCAN_FLIPPER) ||
          (wifi_scan_obj.currentScanMode == BT_ATTACK_SOUR_APPLE) ||
          (wifi_scan_obj.currentScanMode == BT_ATTACK_SWIFTPAIR_SPAM) ||
          (wifi_scan_obj.currentScanMode == BT_ATTACK_SPAM_ALL) ||
          (wifi_scan_obj.currentScanMode == BT_ATTACK_SAMSUNG_SPAM) ||
          (wifi_scan_obj.currentScanMode == BT_ATTACK_GOOGLE_SPAM) ||
          (wifi_scan_obj.currentScanMode == BT_ATTACK_FLIPPER_SPAM) ||
          (wifi_scan_obj.currentScanMode == BT_SPOOF_AIRTAG) ||
          (wifi_scan_obj.currentScanMode == BT_SCAN_WAR_DRIVE) ||
          (wifi_scan_obj.currentScanMode == BT_SCAN_WAR_DRIVE_CONT) ||
          (wifi_scan_obj.currentScanMode == BT_SCAN_SKIMMERS) ||
          (wifi_scan_obj.currentScanMode == BT_SCAN_ANALYZER))
      {
        wifi_scan_obj.StartScan(WIFI_SCAN_OFF);
  
        // If we don't do this, the text and button coordinates will be off
        display_obj.tft.init();
  
        // Take us back to the menu
        changeMenu(current_menu);
      }
  
      x = -1;
      y = -1;
  
      return;
    }
  #endif

  #ifdef HAS_BUTTONS

    #if (C_BTN >= 0) && !defined(MARAUDER_CARDPUTER)
      bool c_btn_press = c_btn.justPressed();
    #elif defined(MARAUDER_CARDPUTER)
      bool c_btn_press = this->isKeyPressed('(');
    #endif

    #ifndef HAS_ILI9341
    
      if ((c_btn_press) &&
          (wifi_scan_obj.currentScanMode != WIFI_SCAN_OFF) &&
          (wifi_scan_obj.currentScanMode != WIFI_CONNECTED) &&
          (wifi_scan_obj.currentScanMode != OTA_UPDATE) &&
          (wifi_scan_obj.currentScanMode != ESP_UPDATE) &&
          (wifi_scan_obj.currentScanMode != SHOW_INFO) &&
          (wifi_scan_obj.currentScanMode != WIFI_SCAN_GPS_DATA) &&
          (wifi_scan_obj.currentScanMode != GPS_POI) &&
          (wifi_scan_obj.currentScanMode != GPS_TRACKER) &&
          (wifi_scan_obj.currentScanMode != WIFI_SCAN_GPS_NMEA))
      {
        // Stop the current scan
        if ((wifi_scan_obj.currentScanMode == WIFI_SCAN_PROBE) ||
            (wifi_scan_obj.currentScanMode == WIFI_SCAN_STATION_WAR_DRIVE) ||
            (wifi_scan_obj.currentScanMode == WIFI_SCAN_RAW_CAPTURE) ||
            (wifi_scan_obj.currentScanMode == WIFI_SCAN_STATION) ||
            (wifi_scan_obj.currentScanMode == WIFI_SCAN_AP) ||
            (wifi_scan_obj.currentScanMode == WIFI_SCAN_WAR_DRIVE) ||
            (wifi_scan_obj.currentScanMode == WIFI_SCAN_EVIL_PORTAL) ||
            (wifi_scan_obj.currentScanMode == WIFI_SCAN_SIG_STREN) ||
            (wifi_scan_obj.currentScanMode == WIFI_SCAN_TARGET_AP) ||
            (wifi_scan_obj.currentScanMode == WIFI_SCAN_TARGET_AP_FULL) ||
            (wifi_scan_obj.currentScanMode == WIFI_SCAN_AP_STA) ||
            (wifi_scan_obj.currentScanMode == WIFI_PING_SCAN) ||
            (wifi_scan_obj.currentScanMode == WIFI_ARP_SCAN) ||
            (wifi_scan_obj.currentScanMode == WIFI_PORT_SCAN_ALL) ||
            (wifi_scan_obj.currentScanMode == WIFI_SCAN_SSH) ||
            (wifi_scan_obj.currentScanMode == WIFI_SCAN_TELNET) ||
            (wifi_scan_obj.currentScanMode == WIFI_SCAN_PWN) ||
            (wifi_scan_obj.currentScanMode == WIFI_SCAN_PINESCAN) ||
            (wifi_scan_obj.currentScanMode == WIFI_SCAN_MULTISSID) ||
            (wifi_scan_obj.currentScanMode == WIFI_SCAN_ESPRESSIF) ||
            (wifi_scan_obj.currentScanMode == WIFI_SCAN_ALL) ||
            (wifi_scan_obj.currentScanMode == WIFI_SCAN_DEAUTH) ||
            (wifi_scan_obj.currentScanMode == WIFI_ATTACK_BEACON_SPAM) ||
            (wifi_scan_obj.currentScanMode == WIFI_ATTACK_AP_SPAM) ||
            (wifi_scan_obj.currentScanMode == WIFI_ATTACK_AUTH) ||
            (wifi_scan_obj.currentScanMode == WIFI_ATTACK_DEAUTH) ||
            (wifi_scan_obj.currentScanMode == WIFI_ATTACK_DEAUTH_MANUAL) ||
            (wifi_scan_obj.currentScanMode == WIFI_ATTACK_DEAUTH_TARGETED) ||
            (wifi_scan_obj.currentScanMode == WIFI_ATTACK_BAD_MSG_TARGETED) ||
            (wifi_scan_obj.currentScanMode == WIFI_ATTACK_BAD_MSG) ||
            (wifi_scan_obj.currentScanMode == WIFI_ATTACK_SLEEP) ||
            (wifi_scan_obj.currentScanMode == WIFI_ATTACK_SLEEP_TARGETED) ||
            (wifi_scan_obj.currentScanMode == WIFI_ATTACK_MIMIC) ||
            (wifi_scan_obj.currentScanMode == WIFI_ATTACK_RICK_ROLL) ||
            (wifi_scan_obj.currentScanMode == WIFI_ATTACK_BEACON_LIST) ||
            (wifi_scan_obj.currentScanMode == BT_SCAN_ALL) ||
            (wifi_scan_obj.currentScanMode == BT_SCAN_AIRTAG) ||
            (wifi_scan_obj.currentScanMode == BT_SCAN_FLIPPER) ||
            (wifi_scan_obj.currentScanMode == BT_ATTACK_SOUR_APPLE) ||
            (wifi_scan_obj.currentScanMode == BT_ATTACK_SWIFTPAIR_SPAM) ||
            (wifi_scan_obj.currentScanMode == BT_ATTACK_SPAM_ALL) ||
            (wifi_scan_obj.currentScanMode == BT_ATTACK_SAMSUNG_SPAM) ||
            (wifi_scan_obj.currentScanMode == BT_ATTACK_GOOGLE_SPAM) ||
            (wifi_scan_obj.currentScanMode == BT_ATTACK_FLIPPER_SPAM) ||
            (wifi_scan_obj.currentScanMode == BT_SPOOF_AIRTAG) ||
            (wifi_scan_obj.currentScanMode == BT_SCAN_WAR_DRIVE) ||
            (wifi_scan_obj.currentScanMode == BT_SCAN_WAR_DRIVE_CONT) ||
            (wifi_scan_obj.currentScanMode == BT_SCAN_SKIMMERS) ||
            (wifi_scan_obj.currentScanMode == WIFI_SCAN_EAPOL) ||
            (wifi_scan_obj.currentScanMode == WIFI_SCAN_ACTIVE_EAPOL) ||
            (wifi_scan_obj.currentScanMode == WIFI_SCAN_ACTIVE_LIST_EAPOL) ||
            (wifi_scan_obj.currentScanMode == WIFI_PACKET_MONITOR) ||
            (wifi_scan_obj.currentScanMode == WIFI_SCAN_CHAN_ANALYZER) ||
            (wifi_scan_obj.currentScanMode == WIFI_SCAN_PACKET_RATE) ||
            (wifi_scan_obj.currentScanMode == BT_SCAN_ANALYZER))
        {
          wifi_scan_obj.StartScan(WIFI_SCAN_OFF);
    
          // If we don't do this, the text and button coordinates will be off
          display_obj.tft.init();
    
          // Take us back to the menu
          changeMenu(current_menu);
        }
    
        x = -1;
        y = -1;
    
        return;
      }
    #endif

  #endif


  // Check if any key coordinate boxes contain the touch coordinates
  // This is for when on a menu
  // Make sure to add certain scanning functions here or else
  // menu items will be selected while scans and attacks are running
  #ifdef HAS_ILI9341
    if ((wifi_scan_obj.currentScanMode != WIFI_ATTACK_BEACON_SPAM) &&
        (wifi_scan_obj.currentScanMode != WIFI_ATTACK_AP_SPAM) &&
        (wifi_scan_obj.currentScanMode != WIFI_ATTACK_AUTH) &&
        (wifi_scan_obj.currentScanMode != WIFI_ATTACK_DEAUTH) &&
        (wifi_scan_obj.currentScanMode != WIFI_ATTACK_DEAUTH_MANUAL) &&
        (wifi_scan_obj.currentScanMode != WIFI_ATTACK_DEAUTH_TARGETED) &&
        (wifi_scan_obj.currentScanMode != WIFI_ATTACK_BAD_MSG_TARGETED) &&
        (wifi_scan_obj.currentScanMode != WIFI_ATTACK_BAD_MSG) &&
        (wifi_scan_obj.currentScanMode != WIFI_ATTACK_SLEEP) &&
        (wifi_scan_obj.currentScanMode != WIFI_ATTACK_SLEEP_TARGETED) &&
        (wifi_scan_obj.currentScanMode != WIFI_ATTACK_MIMIC) &&
        (wifi_scan_obj.currentScanMode != WIFI_SCAN_PACKET_RATE) &&
        (wifi_scan_obj.currentScanMode != WIFI_SCAN_RAW_CAPTURE) &&
        (wifi_scan_obj.currentScanMode != WIFI_SCAN_CHAN_ANALYZER) &&
        (wifi_scan_obj.currentScanMode != WIFI_SCAN_SIG_STREN) &&
        (wifi_scan_obj.currentScanMode != WIFI_ATTACK_RICK_ROLL))
    {
      // Need this to set all keys to false
      /*for (uint8_t b = 0; b < BUTTON_ARRAY_LEN; b++) {
        if (pressed && display_obj.key[b].contains(t_x, t_y)) {
          display_obj.key[b].press(true);  // tell the button it is pressed
        } else {
          display_obj.key[b].press(false);  // tell the button it is NOT pressed
        }
      }*/

      // Detect up, down, select
      uint8_t menu_button = display_obj.menuButton(&t_x, &t_y, pressed);

      if (menu_button > -1) {
        if (menu_button == UP_BUTTON) {
          if ((wifi_scan_obj.currentScanMode == WIFI_SCAN_OFF) ||
              (wifi_scan_obj.currentScanMode == WIFI_CONNECTED) ||
              (wifi_scan_obj.currentScanMode == OTA_UPDATE)) {
            if (current_menu->selected > 0) {
              current_menu->selected--;
              // Page up
              if (current_menu->selected < this->menu_start_index) {
                this->buildButtons(current_menu, current_menu->selected);
                this->displayCurrentMenu(current_menu->selected);
              }
              this->buttonSelected(current_menu->selected - this->menu_start_index, current_menu->selected);
              if (!current_menu->list->get(current_menu->selected + 1).selected)
                this->buttonNotSelected(current_menu->selected + 1 - this->menu_start_index, current_menu->selected + 1);
            }
            // Loop to end
            else {
              current_menu->selected = current_menu->list->size() - 1;
              if (current_menu->selected >= BUTTON_SCREEN_LIMIT) {
                this->buildButtons(current_menu, current_menu->selected + 1 - BUTTON_SCREEN_LIMIT);
                this->displayCurrentMenu(current_menu->selected + 1 - BUTTON_SCREEN_LIMIT);
              }
              this->buttonSelected(current_menu->selected, current_menu->selected);
              if (!current_menu->list->get(0).selected)
                this->buttonNotSelected(0, this->menu_start_index);
            }
          }
          else if ((wifi_scan_obj.currentScanMode == WIFI_PACKET_MONITOR) ||
                  (wifi_scan_obj.currentScanMode == WIFI_SCAN_EAPOL) ||
                  (wifi_scan_obj.currentScanMode == WIFI_SCAN_CHAN_ANALYZER) ||
                  (wifi_scan_obj.currentScanMode == WIFI_SCAN_PACKET_RATE) ||
                  (wifi_scan_obj.currentScanMode == WIFI_SCAN_RAW_CAPTURE) ||
                  (wifi_scan_obj.currentScanMode == WIFI_SCAN_SIG_STREN)) {
            if (wifi_scan_obj.set_channel < 14)
              wifi_scan_obj.changeChannel(wifi_scan_obj.set_channel + 1);
            else
              wifi_scan_obj.changeChannel(1);
          }
        }
        if (menu_button == DOWN_BUTTON) {
          if ((wifi_scan_obj.currentScanMode == WIFI_SCAN_OFF) ||
              (wifi_scan_obj.currentScanMode == WIFI_CONNECTED) ||
              (wifi_scan_obj.currentScanMode == OTA_UPDATE)) {
            if (current_menu->selected < current_menu->list->size() - 1) {
              current_menu->selected++;
              // Page down
              if (current_menu->selected - this->menu_start_index >= BUTTON_SCREEN_LIMIT) {
                this->buildButtons(current_menu, current_menu->selected + 1 - BUTTON_SCREEN_LIMIT);
                this->displayCurrentMenu(current_menu->selected + 1 - BUTTON_SCREEN_LIMIT);
              }
              else
                this->buttonSelected(current_menu->selected - this->menu_start_index, current_menu->selected);
              if (!current_menu->list->get(current_menu->selected - 1).selected)
                this->buttonNotSelected(current_menu->selected - 1 - this->menu_start_index, current_menu->selected - 1);
            }
            // Loop to beginning
            else {
              if (current_menu->selected >= BUTTON_SCREEN_LIMIT) {
                current_menu->selected = 0;
                this->buildButtons(current_menu);
                this->displayCurrentMenu();
                this->buttonSelected(current_menu->selected);
              }
              else {
                current_menu->selected = 0;
                this->buttonSelected(current_menu->selected);
                if (!current_menu->list->get(current_menu->list->size() - 1).selected)
                  this->buttonNotSelected(current_menu->list->size() - 1);
              }
            }
          }
          else if ((wifi_scan_obj.currentScanMode == WIFI_PACKET_MONITOR) ||
                  (wifi_scan_obj.currentScanMode == WIFI_SCAN_EAPOL) ||
                  (wifi_scan_obj.currentScanMode == WIFI_SCAN_CHAN_ANALYZER) ||
                  (wifi_scan_obj.currentScanMode == WIFI_SCAN_PACKET_RATE) ||
                  (wifi_scan_obj.currentScanMode == WIFI_SCAN_RAW_CAPTURE) ||
                  (wifi_scan_obj.currentScanMode == WIFI_SCAN_SIG_STREN)) {
            if (wifi_scan_obj.set_channel > 1)
              wifi_scan_obj.changeChannel(wifi_scan_obj.set_channel - 1);
            else
              wifi_scan_obj.changeChannel(14);
          }
        }
        if(menu_button == SELECT_BUTTON) {
          current_menu->list->get(current_menu->selected).callable();
        }
        else {
          if ((wifi_scan_obj.currentScanMode == WIFI_SCAN_OFF) ||
              (wifi_scan_obj.currentScanMode == WIFI_CONNECTED))
            this->displayMenuButtons();
        }
      }
  
      // Check if any key has changed state
      /*for (uint8_t b = 0; b < current_menu->list->size(); b++) {
        display_obj.tft.setFreeFont(MENU_FONT);
        if (display_obj.key[b].justPressed()) {
          display_obj.key[b].drawButton(true, current_menu->list->get(b).name);
          if (current_menu->list->get(b).name != text09)
            display_obj.tft.drawXBitmap(0,
                                        KEY_Y + b * (KEY_H + KEY_SPACING_Y) - (ICON_H / 2),
                                        menu_icons[current_menu->list->get(b).icon],
                                        ICON_W,
                                        ICON_H,
                                        this->getColor(current_menu->list->get(b).color),
                                        TFT_BLACK);
        }
  
        // If button was just release, execute the button's function
        if ((display_obj.key[b].justReleased()) && (!pressed))
        {
          display_obj.key[b].drawButton(false, current_menu->list->get(b).name);
          current_menu->list->get(b).callable();
        }
        // This
        else if ((display_obj.key[b].justReleased()) && (pressed)) {
          display_obj.key[b].drawButton(false, current_menu->list->get(b).name);
          if (current_menu->list->get(b).name != text09)
            display_obj.tft.drawXBitmap(0,
                                        KEY_Y + b * (KEY_H + KEY_SPACING_Y) - (ICON_H / 2),
                                        menu_icons[current_menu->list->get(b).icon],
                                        ICON_W,
                                        ICON_H,
                                        TFT_BLACK,
                                        this->getColor(current_menu->list->get(b).color));
        }
  
        display_obj.tft.setFreeFont(NULL);
      }*/
    }
    x = -1;
    y = -1;
  #endif

  // Menu navigation and paging
  #ifdef HAS_BUTTONS
    // Don't do this for touch screens
    #if !(defined(MARAUDER_V6) || defined(MARAUDER_V6_1) || defined(MARAUDER_CYD_MICRO) || defined(MARAUDER_CYD_GUITION) || defined(MARAUDER_CYD_2USB))
      #if !defined(MARAUDER_M5STICKC) || defined(MARAUDER_M5STICKCP2)
        #if (U_BTN >= 0 || defined(MARAUDER_CARDPUTER))
          #if (U_BTN >= 0)
            if (u_btn.justPressed()) {
          #elif defined(MARAUDER_CARDPUTER)
            if (this->isKeyPressed(';')) {
          #endif
              if ((wifi_scan_obj.currentScanMode == WIFI_SCAN_OFF) ||
                  (wifi_scan_obj.currentScanMode == WIFI_CONNECTED) ||
                  (wifi_scan_obj.currentScanMode == OTA_UPDATE)) {
                if (current_menu->selected > 0) {
                  current_menu->selected--;
                  // Page up
                  if (current_menu->selected < this->menu_start_index) {
                    this->buildButtons(current_menu, current_menu->selected);
                    this->displayCurrentMenu(current_menu->selected);
                  }
                  this->buttonSelected(current_menu->selected - this->menu_start_index, current_menu->selected);
                  if (!current_menu->list->get(current_menu->selected + 1).selected)
                    this->buttonNotSelected(current_menu->selected + 1 - this->menu_start_index, current_menu->selected + 1);
                }
                // Loop to end
                else {
                  current_menu->selected = current_menu->list->size() - 1;
                  if (current_menu->selected >= BUTTON_SCREEN_LIMIT) {
                    this->buildButtons(current_menu, current_menu->selected + 1 - BUTTON_SCREEN_LIMIT);
                    this->displayCurrentMenu(current_menu->selected + 1 - BUTTON_SCREEN_LIMIT);
                  }
                  this->buttonSelected(current_menu->selected, current_menu->selected);
                  if (!current_menu->list->get(0).selected)
                    this->buttonNotSelected(0, this->menu_start_index);
                }
              }
              else if ((wifi_scan_obj.currentScanMode == WIFI_PACKET_MONITOR) ||
                      (wifi_scan_obj.currentScanMode == WIFI_SCAN_EAPOL) ||
                      (wifi_scan_obj.currentScanMode == WIFI_SCAN_CHAN_ANALYZER) ||
                      (wifi_scan_obj.currentScanMode == WIFI_SCAN_PACKET_RATE) ||
                      (wifi_scan_obj.currentScanMode == WIFI_SCAN_RAW_CAPTURE) ||
                      (wifi_scan_obj.currentScanMode == WIFI_SCAN_SIG_STREN)) {
                if (wifi_scan_obj.set_channel < 14)
                  wifi_scan_obj.changeChannel(wifi_scan_obj.set_channel + 1);
                else
                  wifi_scan_obj.changeChannel(1);
              }
            }
        #endif
      #endif

      #if (D_BTN >= 0 || defined(MARAUDER_CARDPUTER))
      #if (D_BTN >= 0)
      if (d_btn.justPressed()){
      #elif defined(MARAUDER_CARDPUTER)
      if (this->isKeyPressed('.')){
      #endif
        if ((wifi_scan_obj.currentScanMode == WIFI_SCAN_OFF) ||
            (wifi_scan_obj.currentScanMode == WIFI_CONNECTED) ||
            (wifi_scan_obj.currentScanMode == OTA_UPDATE)) {
          if (current_menu->selected < current_menu->list->size() - 1) {
            current_menu->selected++;
            // Page down
            if (current_menu->selected - this->menu_start_index >= BUTTON_SCREEN_LIMIT) {
              this->buildButtons(current_menu, current_menu->selected + 1 - BUTTON_SCREEN_LIMIT);
              this->displayCurrentMenu(current_menu->selected + 1 - BUTTON_SCREEN_LIMIT);
            }
            else
              this->buttonSelected(current_menu->selected - this->menu_start_index, current_menu->selected);
            if (!current_menu->list->get(current_menu->selected - 1).selected)
              this->buttonNotSelected(current_menu->selected - 1 - this->menu_start_index, current_menu->selected - 1);
          }
          // Loop to beginning
          else {
            if (current_menu->selected >= BUTTON_SCREEN_LIMIT) {
              current_menu->selected = 0;
              this->buildButtons(current_menu);
              this->displayCurrentMenu();
              this->buttonSelected(current_menu->selected);
            }
            else {
              current_menu->selected = 0;
              this->buttonSelected(current_menu->selected);
              if (!current_menu->list->get(current_menu->list->size() - 1).selected)
                this->buttonNotSelected(current_menu->list->size() - 1);
            }
          }
        }
        else if ((wifi_scan_obj.currentScanMode == WIFI_PACKET_MONITOR) ||
                (wifi_scan_obj.currentScanMode == WIFI_SCAN_EAPOL) ||
                (wifi_scan_obj.currentScanMode == WIFI_SCAN_CHAN_ANALYZER) ||
                (wifi_scan_obj.currentScanMode == WIFI_SCAN_PACKET_RATE) ||
                (wifi_scan_obj.currentScanMode == WIFI_SCAN_RAW_CAPTURE) ||
                (wifi_scan_obj.currentScanMode == WIFI_SCAN_SIG_STREN)) {
          if (wifi_scan_obj.set_channel > 1)
            wifi_scan_obj.changeChannel(wifi_scan_obj.set_channel - 1);
          else
            wifi_scan_obj.changeChannel(14);
        }
      }
      #endif

      #if (R_BTN >= 0 || defined(MARAUDER_CARDPUTER))
      #if (R_BTN >= 0)
      if (r_btn.justPressed()) {
      #elif defined(MARAUDER_CARDPUTER)
      if (this->isKeyPressed('/')) {
      #endif
        if (wifi_scan_obj.currentScanMode == WIFI_SCAN_OFF) {
          if (wifi_scan_obj.set_channel < 14)
            wifi_scan_obj.changeChannel(wifi_scan_obj.set_channel + 1);
          else
            wifi_scan_obj.changeChannel(1);
        }
      }
      #endif

      #if (L_BTN >= 0 || defined(MARAUDER_CARDPUTER))
      #if (L_BTN >= 0)
      if (l_btn.justPressed()) {
      #elif defined(MARAUDER_CARDPUTER)
      if (this->isKeyPressed(',')) {
      #endif
        if (wifi_scan_obj.currentScanMode == WIFI_SCAN_OFF) {
          if (wifi_scan_obj.set_channel > 1)
            wifi_scan_obj.changeChannel(wifi_scan_obj.set_channel - 1);
          else
            wifi_scan_obj.changeChannel(14);
        }
      }
      #endif

      if(c_btn_press){
        current_menu->list->get(current_menu->selected).callable();
      }

    #endif
  #endif
}

#if BATTERY_ANALOG_ON == 1
byte battery_analog_array[10];
byte battery_count = 0;
byte battery_analog_last = 101;
#define BATTERY_CHECK 50
uint16_t battery_analog = 0;
void MenuFunctions::battery(bool initial)
{
  if (BATTERY_ANALOG_ON) {
    uint8_t n = 0;
    byte battery_analog_sample[10];
    byte deviation;
    if (battery_count == BATTERY_CHECK - 5)  digitalWrite(BATTERY_PIN, HIGH);
    else if (battery_count == 5) digitalWrite(BATTERY_PIN, LOW);
    if (battery_count == 0) {
      battery_analog = 0;
      for (n = 9; n > 0; n--)battery_analog_array[n] = battery_analog_array[n - 1];
      for (n = 0; n < 10; n++) {
        battery_analog_sample[n] = map((analogRead(ANALOG_PIN) * 5), 2400, 4200, 0, 100);
        if (battery_analog_sample[n] > 100) battery_analog_sample[n] = 100;
        else if (battery_analog_sample[n] < 0) battery_analog_sample[n] = 0;
        battery_analog += battery_analog_sample[n];
      }
      battery_analog = battery_analog / 10;
      for (n = 0; n < 10; n++) {
        deviation = abs(battery_analog - battery_analog_sample[n]);
        if (deviation >= 10) battery_analog_sample[n] = battery_analog;
      }
      battery_analog = 0;
      for (n = 0; n < 10; n++) battery_analog += battery_analog_sample[n];
      battery_analog = battery_analog / 10;
      battery_analog_array[0] = battery_analog;
      if (battery_analog_array[9] > 0 ) {
        battery_analog = 0;
        for (n = 0; n < 10; n++) battery_analog += battery_analog_array[n];
        battery_analog = battery_analog / 10;
      }
      battery_count ++;
    }
    else if (battery_count < BATTERY_CHECK) battery_count++;
    else if (battery_count >= BATTERY_CHECK) battery_count = 0;

    if (battery_analog_last != battery_analog) {
      battery_analog_last = battery_analog;
      MenuFunctions::battery2();
    }
  }
}
void MenuFunctions::battery2(bool initial)
{
  uint16_t the_color;
  if ( digitalRead(CHARGING_PIN) == 1) the_color = TFT_BLUE;
  else if (battery_analog < 20) the_color = TFT_RED;
  else if (battery_analog < 40)  the_color = TFT_YELLOW;
  else the_color = TFT_GREEN;

  display_obj.tft.setTextColor(the_color, STATUSBAR_COLOR);
  display_obj.tft.fillRect(186, 0, 50, STATUS_BAR_WIDTH, STATUSBAR_COLOR);
  display_obj.tft.drawXBitmap(186,
                              0,
                              menu_icons[STATUS_BAT],
                              16,
                              16,
                              STATUSBAR_COLOR,
                              the_color);
  display_obj.tft.drawString((String) battery_analog + "%", 204, 0, 2);
}
#else
void MenuFunctions::battery(bool initial)
{
  #ifdef HAS_BATTERY
    uint16_t the_color;
    if (battery_obj.i2c_supported)
    {
      // Could use int compare maybe idk
      if (((String)battery_obj.battery_level != "25") && ((String)battery_obj.battery_level != "0"))
        the_color = TFT_GREEN;
      else
        the_color = TFT_RED;

      if ((battery_obj.battery_level != battery_obj.old_level) || (initial)) {
        battery_obj.old_level = battery_obj.battery_level;
        display_obj.tft.fillRect(204, 0, SCREEN_WIDTH, STATUS_BAR_WIDTH, STATUSBAR_COLOR);
      }

      display_obj.tft.setCursor(0, 1);
      /*if (!this->disable_touch) {
        display_obj.tft.drawXBitmap(186,
                                    0,
                                    menu_icons[STATUS_BAT],
                                    16,
                                    16,
                                    STATUSBAR_COLOR,
                                    the_color);
      }*/
      display_obj.tft.drawString((String)battery_obj.battery_level + "%", 204, 0, 2);
    }
  #endif
}
void MenuFunctions::battery2(bool initial)
{
  MenuFunctions::battery(initial);
}
#endif

void MenuFunctions::updateStatusBar()
{
  display_obj.tft.setTextSize(1);

  bool status_changed = false;
  
  #if defined(MARAUDER_MINI) || defined(MARAUDER_M5STICKC) || defined(MARAUDER_REV_FEATHER) || defined(MARAUDER_CARDPUTER)
    display_obj.tft.setFreeFont(NULL);
  #endif
  
  uint16_t the_color; 

  #ifdef HAS_GPS
    if (this->old_gps_sat_count != gps_obj.getNumSats()) {
      this->old_gps_sat_count = gps_obj.getNumSats();
      display_obj.tft.fillRect(0, 0, 240, STATUS_BAR_WIDTH, STATUSBAR_COLOR);
      status_changed = true;
    }
  #endif

  // GPS Stuff
  #ifdef HAS_GPS
    if (gps_obj.getGpsModuleStatus()) {
      if (gps_obj.getFixStatus())
        the_color = TFT_GREEN;
      else
        the_color = TFT_RED;
        
      #ifdef HAS_FULL_SCREEN
        display_obj.tft.drawXBitmap(4,
                                    0,
                                    menu_icons[STATUS_GPS],
                                    16,
                                    16,
                                    STATUSBAR_COLOR,
                                    the_color);
        display_obj.tft.setTextColor(TFT_WHITE, STATUSBAR_COLOR);

        display_obj.tft.drawString(gps_obj.getNumSatsString(), 22, 0, 2);
      #elif defined(HAS_SCREEN)
        display_obj.tft.setTextColor(the_color, STATUSBAR_COLOR);
        display_obj.tft.drawString("GPS", 0, 0, 1);
      #endif
    }
  #endif

  display_obj.tft.setTextColor(TFT_WHITE, STATUSBAR_COLOR);

  // WiFi Channel Stuff
  uint8_t primaryChannel;
  wifi_second_chan_t secondChannel;
  esp_err_t err = esp_wifi_get_channel(&primaryChannel, &secondChannel);

  uint8_t current_channel = wifi_scan_obj.set_channel;

  if (err == ESP_OK)
    current_channel = primaryChannel;

  if ((current_channel != wifi_scan_obj.old_channel) || (status_changed)) {
    wifi_scan_obj.old_channel = current_channel;
    #if defined(MARAUDER_MINI) || defined(MARAUDER_M5STICKC) || defined(MARAUDER_REV_FEATHER) || defined(MARAUDER_CARDPUTER)
      display_obj.tft.fillRect(43, 0, TFT_WIDTH * 0.21, STATUS_BAR_WIDTH, STATUSBAR_COLOR);
    #else
      display_obj.tft.fillRect(50, 0, TFT_WIDTH * 0.21, STATUS_BAR_WIDTH, STATUSBAR_COLOR);
    #endif
    #ifdef HAS_FULL_SCREEN
      display_obj.tft.drawString("CH: " + (String)wifi_scan_obj.old_channel, 50, 0, 2);
    #endif

    #ifdef HAS_MINI_SCREEN
      display_obj.tft.drawString("CH: " + (String)wifi_scan_obj.old_channel, TFT_WIDTH/4, 0, 1);
    #endif
  }

  // RAM Stuff
  wifi_scan_obj.freeRAM();
  if ((wifi_scan_obj.free_ram != wifi_scan_obj.old_free_ram) || (status_changed)) {
    wifi_scan_obj.old_free_ram = wifi_scan_obj.free_ram;
    display_obj.tft.fillRect(100, 0, 60, STATUS_BAR_WIDTH, STATUSBAR_COLOR);
    #ifdef HAS_FULL_SCREEN
    //display_obj.tft.setCursor(100, 0);
    //display_obj.tft.setFreeFont(2);
    //display_obj.tft.print("D:" + String(getDRAMUsagePercent()) + "%");
    #ifndef HAS_PSRAM
      display_obj.tft.drawString("D:" + String(getDRAMUsagePercent()) + "%", 100, 0, 2);
    #else
      //display_obj.tft.drawString("D:" + String(getDRAMUsagePercent()) + "%" + " P:" + String(getPSRAMUsagePercent()) + "%", 100, 0, 1);
      display_obj.tft.drawString("D:" + String(getDRAMUsagePercent()) + "%", 100, 0, 1);
      display_obj.tft.drawString("P:" + String(getPSRAMUsagePercent()) + "%", 100, 8, 1);
    #endif
    //display_obj.tft.drawString((String)wifi_scan_obj.free_ram + "B", 100, 0, 2);
  #endif

  #ifdef HAS_MINI_SCREEN
    //display_obj.tft.setCursor(TFT_WIDTH/1.75, 0);
    //display_obj.tft.setFreeFont(1);
    //display_obj.tft.print("D:" + String(getDRAMUsagePercent()) + "%");
    #ifndef HAS_PSRAM
      display_obj.tft.drawString("D:" + String(getDRAMUsagePercent()) + "%", TFT_WIDTH/1.75, 0, 1);
    #else
      display_obj.tft.drawString("D:" + String(getDRAMUsagePercent()) + "%" + " P:" + String(getPSRAMUsagePercent()) + "%", TFT_WIDTH/1.75, 0, 1);
    #endif
    //display_obj.tft.drawString((String)wifi_scan_obj.free_ram + "B", TFT_WIDTH/1.75, 0, 1);
  #endif
  }

  // Draw battery info
  MenuFunctions::battery(false);
  display_obj.tft.fillRect(186, 0, 16, STATUS_BAR_WIDTH, STATUSBAR_COLOR);

  // Disable touch stuff
  #ifdef HAS_ILI9341
    #ifdef HAS_BUTTONS
      if (this->disable_touch) {
        display_obj.tft.setCursor(0, 1);
        display_obj.tft.drawXBitmap(186,
                                    0,
                                    menu_icons[DISABLE_TOUCH],
                                    16,
                                    16,
                                    STATUSBAR_COLOR,
                                    TFT_RED);
      }
      else {
        display_obj.tft.setCursor(0, 1);
        display_obj.tft.drawXBitmap(186,
                                    0,
                                    menu_icons[DISABLE_TOUCH],
                                    16,
                                    16,
                                    STATUSBAR_COLOR,
                                    TFT_DARKGREY);
      }
    #endif
  #endif

  // Draw SD info
  #ifdef HAS_SD
    if (sd_obj.supported)
      the_color = TFT_GREEN;
    else
      the_color = TFT_RED;

    #ifdef HAS_FULL_SCREEN
      display_obj.tft.drawXBitmap(170,
                                  0,
                                  menu_icons[STATUS_SD],
                                  16,
                                  16,
                                  STATUSBAR_COLOR,
                                  the_color);
    #endif
  #endif

  #ifdef HAS_MINI_SCREEN
    display_obj.tft.setTextColor(the_color, STATUSBAR_COLOR);
    display_obj.tft.drawString("SD", TFT_WIDTH - 12, 0, 1);
  #endif

  // WiFi connection status stuff
  if (wifi_scan_obj.wifi_connected) {
    #ifdef HAS_FULL_SCREEN
      display_obj.tft.drawXBitmap(170 - 16,
                                  0,
                                  menu_icons[JOINED],
                                  16,
                                  16,
                                  STATUSBAR_COLOR,
                                  TFT_GREEN);
    #endif
  } else {
    #ifdef HAS_FULL_SCREEN
      display_obj.tft.drawXBitmap(170 - 16,
                                  0,
                                  menu_icons[JOINED],
                                  16,
                                  16,
                                  STATUSBAR_COLOR,
                                  TFT_DARKGREY);
    #endif
  }

  // Force PMKID stuff
  if ((wifi_scan_obj.force_pmkid) || (wifi_scan_obj.ep_deauth)) {
    #ifdef HAS_FULL_SCREEN
      display_obj.tft.drawXBitmap(170 - (16 * 2),
                                  0,
                                  menu_icons[FORCE],
                                  16,
                                  16,
                                  STATUSBAR_COLOR,
                                  TFT_GREEN);
    #endif
  } else {
    #ifdef HAS_FULL_SCREEN
      display_obj.tft.drawXBitmap(170 - (16 * 2),
                                  0,
                                  menu_icons[FORCE],
                                  16,
                                  16,
                                  STATUSBAR_COLOR,
                                  TFT_DARKGREY);
    #endif
  }
}

void MenuFunctions::drawStatusBar()
{
  display_obj.tft.setTextSize(1);
  #ifdef HAS_MINI_SCREEN
    display_obj.tft.setFreeFont(NULL);
  #endif
  display_obj.tft.fillRect(0, 0, 240, STATUS_BAR_WIDTH, STATUSBAR_COLOR);
  display_obj.tft.setTextColor(TFT_WHITE, STATUSBAR_COLOR);

  uint16_t the_color;

  // GPS Stuff
  #ifdef HAS_GPS
    if (gps_obj.getGpsModuleStatus()) {
      if (gps_obj.getFixStatus())
        the_color = TFT_GREEN;
      else
        the_color = TFT_RED;
        
      #ifdef HAS_FULL_SCREEN
        display_obj.tft.drawXBitmap(4,
                                    0,
                                    menu_icons[STATUS_GPS],
                                    16,
                                    16,
                                    STATUSBAR_COLOR,
                                    the_color);
        display_obj.tft.setTextColor(TFT_WHITE, STATUSBAR_COLOR);

        display_obj.tft.drawString(gps_obj.getNumSatsString(), 22, 0, 2);
      #endif
    }
  #endif

  display_obj.tft.setTextColor(TFT_WHITE, STATUSBAR_COLOR);


  // WiFi Channel Stuff
  uint8_t primaryChannel;
  wifi_second_chan_t secondChannel;
  esp_err_t err = esp_wifi_get_channel(&primaryChannel, &secondChannel);

  if (err == ESP_OK)
    wifi_scan_obj.old_channel = primaryChannel;
  else
    wifi_scan_obj.old_channel = wifi_scan_obj.set_channel;

  #ifdef HAS_MINI_SCREEN
    display_obj.tft.fillRect(43, 0, TFT_WIDTH * 0.21, STATUS_BAR_WIDTH, STATUSBAR_COLOR);
  #else
    display_obj.tft.fillRect(50, 0, TFT_WIDTH * 0.21, STATUS_BAR_WIDTH, STATUSBAR_COLOR);
  #endif
  #ifdef HAS_FULL_SCREEN
    display_obj.tft.drawString("CH: " + (String)wifi_scan_obj.old_channel, 50, 0, 2);
  #endif

  #ifdef HAS_MINI_SCREEN
    display_obj.tft.drawString("CH: " + (String)wifi_scan_obj.old_channel, TFT_WIDTH/4, 0, 1);
  #endif

  // RAM Stuff
  wifi_scan_obj.freeRAM();
  wifi_scan_obj.old_free_ram = wifi_scan_obj.free_ram;
  display_obj.tft.fillRect(100, 0, 60, STATUS_BAR_WIDTH, STATUSBAR_COLOR);
  #ifdef HAS_FULL_SCREEN
    //display_obj.tft.setCursor(100, 0);
    //display_obj.tft.setFreeFont(2);
    //display_obj.tft.print("D:" + String(getDRAMUsagePercent()) + "%");
    #ifndef HAS_PSRAM
      display_obj.tft.drawString("D:" + String(getDRAMUsagePercent()) + "%", 100, 0, 2);
    #else
      //display_obj.tft.drawString("D:" + String(getDRAMUsagePercent()) + "%" + " P:" + String(getPSRAMUsagePercent()) + "%", 100, 0, 1);
      display_obj.tft.drawString("D:" + String(getDRAMUsagePercent()) + "%", 100, 0, 1);
      display_obj.tft.drawString("P:" + String(getPSRAMUsagePercent()) + "%", 100, 8, 1);
    #endif
    //display_obj.tft.drawString((String)wifi_scan_obj.free_ram + "B", 100, 0, 2);
  #endif

  #ifdef HAS_MINI_SCREEN
    //display_obj.tft.setCursor(TFT_WIDTH/1.75, 0);
    //display_obj.tft.setFreeFont(1);
    //display_obj.tft.print("D:" + String(getDRAMUsagePercent()) + "%");
    #ifndef HAS_PSRAM
      display_obj.tft.drawString("D:" + String(getDRAMUsagePercent()) + "%", TFT_WIDTH/1.75, 0, 1);
    #else
      display_obj.tft.drawString("D:" + String(getDRAMUsagePercent()) + "%" + " P:" + String(getPSRAMUsagePercent()) + "%", TFT_WIDTH/1.75, 0, 1);
    #endif
    //display_obj.tft.drawString((String)wifi_scan_obj.free_ram + "B", TFT_WIDTH/1.75, 0, 1);
  #endif


  MenuFunctions::battery(true);
  display_obj.tft.fillRect(186, 0, 16, STATUS_BAR_WIDTH, STATUSBAR_COLOR);


  // Disable touch stuff
  #ifdef HAS_ILI9341
    #ifdef HAS_BUTTONS
      if (this->disable_touch) {
        display_obj.tft.setCursor(0, 1);
        display_obj.tft.drawXBitmap(186,
                                    0,
                                    menu_icons[DISABLE_TOUCH],
                                    16,
                                    16,
                                    STATUSBAR_COLOR,
                                    TFT_RED);
      }
      else {
        display_obj.tft.setCursor(0, 1);
        display_obj.tft.drawXBitmap(186,
                                    0,
                                    menu_icons[DISABLE_TOUCH],
                                    16,
                                    16,
                                    STATUSBAR_COLOR,
                                    TFT_DARKGREY);
      }
    #endif
  #endif

  // Draw SD info
  #ifdef HAS_SD
    if (sd_obj.supported)
      the_color = TFT_GREEN;
    else
      the_color = TFT_RED;
  

    #ifdef HAS_FULL_SCREEN
      display_obj.tft.drawXBitmap(170,
                                  0,
                                  menu_icons[STATUS_SD],
                                  16,
                                  16,
                                  STATUSBAR_COLOR,
                                  the_color);
    #endif
  #endif

  #ifdef HAS_MINI_SCREEN
    display_obj.tft.setTextColor(the_color, STATUSBAR_COLOR);
    display_obj.tft.drawString("SD", TFT_WIDTH - 12, 0, 1);
  #endif

  // WiFi connection status stuff
  if (wifi_scan_obj.wifi_connected) {
    #ifdef HAS_FULL_SCREEN
      display_obj.tft.drawXBitmap(170 - 16,
                                  0,
                                  menu_icons[JOINED],
                                  16,
                                  16,
                                  STATUSBAR_COLOR,
                                  TFT_GREEN);
    #endif
  } else {
    #ifdef HAS_FULL_SCREEN
      display_obj.tft.drawXBitmap(170 - 16,
                                  0,
                                  menu_icons[JOINED],
                                  16,
                                  16,
                                  STATUSBAR_COLOR,
                                  TFT_DARKGREY);
    #endif
  }

  // Force PMKID stuff
  if ((wifi_scan_obj.force_pmkid) || (wifi_scan_obj.ep_deauth)) {
    #ifdef HAS_FULL_SCREEN
      display_obj.tft.drawXBitmap(170 - (16 * 2),
                                  0,
                                  menu_icons[FORCE],
                                  16,
                                  16,
                                  STATUSBAR_COLOR,
                                  TFT_GREEN);
    #endif
  } else {
    #ifdef HAS_FULL_SCREEN
      display_obj.tft.drawXBitmap(170 - (16 * 2),
                                  0,
                                  menu_icons[FORCE],
                                  16,
                                  16,
                                  STATUSBAR_COLOR,
                                  TFT_DARKGREY);
    #endif
  }
}

void MenuFunctions::orientDisplay()
{
  display_obj.tft.init();

  display_obj.tft.setRotation(SCREEN_ORIENTATION); // Portrait

  display_obj.tft.setCursor(0, 0);

  #ifdef HAS_ILI9341
    #ifndef HAS_CYD_TOUCH
      #ifdef TFT_SHIELD
        uint16_t calData[5] = { 275, 3494, 361, 3528, 4 }; // tft.setRotation(0); // Portrait with TFT Shield
      #else if defined(TFT_DIY)
        uint16_t calData[5] = { 339, 3470, 237, 3438, 2 }; // tft.setRotation(0); // Portrait with DIY TFT
      #endif

      display_obj.tft.setTouch(calData);
    #else
      display_obj.touchscreen.setRotation(0);
    #endif
  #endif

  changeMenu(current_menu);
}

void MenuFunctions::runBoolSetting(String key) {
  display_obj.tftDrawRedOnOffButton();
}

String MenuFunctions::callSetting(String key) {
  specSettingMenu.name = key;
  
  String setting_type = settings_obj.getSettingType(key);

  if (setting_type == "bool") {
    return "bool";
  }
}

void MenuFunctions::displaySetting(String key, Menu* menu, int index) {
  specSettingMenu.name = key;

  bool setting_value = settings_obj.loadSetting<bool>(key);

  // Make a local copy of menu node
  MenuNode node = menu->list->get(index);

  display_obj.tft.setTextWrap(false);
  display_obj.tft.setFreeFont(NULL);
  display_obj.tft.setCursor(0, 100);
  display_obj.tft.setTextSize(1);

  // Set local copy value
  if (!setting_value) {
    display_obj.tft.setTextColor(TFT_RED);
    display_obj.tft.println(F(text_table1[4]));
    node.selected = false;
  }
  else {
    display_obj.tft.setTextColor(TFT_GREEN);
    display_obj.tft.println(F(text_table1[5]));
    node.selected = true;
  }

  // Put local copy back into menu
  menu->list->set(index, node);
    
}

#ifdef MARAUDER_CARDPUTER
bool MenuFunctions::isKeyPressed(char c)
{
  M5CardputerKeyboard.updateKeyList();
  M5CardputerKeyboard.updateKeysState();
  bool pressed = M5CardputerKeyboard.isKeyPressed(c);

  if (pressed)
    delay(200);

  return pressed;
}
#endif

// Function to build the menus
void MenuFunctions::RunSetup()
{
  extern LinkedList<AccessPoint>* access_points;
  extern LinkedList<Station>* stations;
  extern LinkedList<AirTag>* airtags;
  extern LinkedList<IPAddress>* ipList;
  extern LinkedList<ProbeReqSsid>* probe_req_ssids;
  extern LinkedList<ssid>* ssids;

  this->disable_touch = false;
  
  #ifdef HAS_ILI9341
    this->initLVGL();
  #endif

  #ifdef MARAUDER_CARDPUTER
    M5CardputerKeyboard.begin();
  #endif
   
  // root menu stuff
  mainMenu.list = new LinkedList<MenuNode>(); // Get list in first menu ready

  // Main menu stuff
  wifiMenu.list = new LinkedList<MenuNode>(); // Get list in second menu ready
  bluetoothMenu.list = new LinkedList<MenuNode>(); // Get list in third menu ready
  deviceMenu.list = new LinkedList<MenuNode>();
  #ifdef HAS_GPS
    if (gps_obj.getGpsModuleStatus()) {
      gpsMenu.list = new LinkedList<MenuNode>();
      gpsInfoMenu.list = new LinkedList<MenuNode>();
    }
  #endif

  // Device menu stuff
  failedUpdateMenu.list = new LinkedList<MenuNode>();
  whichUpdateMenu.list = new LinkedList<MenuNode>();
  confirmMenu.list = new LinkedList<MenuNode>();
  updateMenu.list = new LinkedList<MenuNode>();
  settingsMenu.list = new LinkedList<MenuNode>();
  specSettingMenu.list = new LinkedList<MenuNode>();
  infoMenu.list = new LinkedList<MenuNode>();
  languageMenu.list = new LinkedList<MenuNode>();

  // WiFi menu stuff
  wifiSnifferMenu.list = new LinkedList<MenuNode>();
  wifiScannerMenu.list = new LinkedList<MenuNode>();
  wifiAttackMenu.list = new LinkedList<MenuNode>();
  #ifdef HAS_GPS
    wardrivingMenu.list = new LinkedList<MenuNode>();
  #endif
  wifiGeneralMenu.list = new LinkedList<MenuNode>();
  wifiAPMenu.list = new LinkedList<MenuNode>();
  wifiIPMenu.list = new LinkedList<MenuNode>();
  apInfoMenu.list = new LinkedList<MenuNode>();
  setMacMenu.list = new LinkedList<MenuNode>();
  genAPMacMenu.list = new LinkedList<MenuNode>();
  #ifdef HAS_BT
    airtagMenu.list = new LinkedList<MenuNode>();
  #endif
  //#ifndef HAS_ILI9341
    wifiStationMenu.list = new LinkedList<MenuNode>();
  //#endif
  selectProbeSSIDsMenu.list = new LinkedList<MenuNode>();

  // WiFi HTML menu stuff
  htmlMenu.list = new LinkedList<MenuNode>();
  //#if (!defined(HAS_ILI9341) && defined(HAS_BUTTONS))
    miniKbMenu.list = new LinkedList<MenuNode>();
  //#endif
  //#ifndef HAS_ILI9341
  //  #ifdef HAS_BUTTONS
      #ifdef HAS_SD
        sdDeleteMenu.list = new LinkedList<MenuNode>();
      #endif
  //  #endif
  //#endif

  // Bluetooth menu stuff
  bluetoothSnifferMenu.list = new LinkedList<MenuNode>();
  bluetoothAttackMenu.list = new LinkedList<MenuNode>();

  // Settings stuff
  generateSSIDsMenu.list = new LinkedList<MenuNode>();
  clearSSIDsMenu.list = new LinkedList<MenuNode>();
  clearAPsMenu.list = new LinkedList<MenuNode>();
  saveFileMenu.list = new LinkedList<MenuNode>();

  saveSSIDsMenu.list = new LinkedList<MenuNode>();
  loadSSIDsMenu.list = new LinkedList<MenuNode>();
  saveAPsMenu.list = new LinkedList<MenuNode>();
  loadAPsMenu.list = new LinkedList<MenuNode>();
  saveATsMenu.list = new LinkedList<MenuNode>();
  loadATsMenu.list = new LinkedList<MenuNode>();

  evilPortalMenu.list = new LinkedList<MenuNode>();
  ssidsMenu.list = new LinkedList<MenuNode>();

  gpsPOIMenu.list = new LinkedList<MenuNode>();

  // Work menu names
  mainMenu.name = text_table1[6];
  wifiMenu.name = text_table1[7];
  deviceMenu.name = text_table1[9];
  failedUpdateMenu.name = text_table1[11];
  whichUpdateMenu.name = text_table1[12];
  confirmMenu.name = text_table1[13];
  updateMenu.name = text_table1[15];
  languageMenu.name = text_table1[16]; 
  infoMenu.name = text_table1[17];
  settingsMenu.name = text_table1[18];
  bluetoothMenu.name = text_table1[19];
  wifiSnifferMenu.name = text_table1[20];
  wifiScannerMenu.name = "Scanners";
  wifiAttackMenu.name = text_table1[21];
  wifiGeneralMenu.name = text_table1[22];
  saveFileMenu.name = "Save/Load Files";
  saveSSIDsMenu.name = "Save SSIDs";
  loadSSIDsMenu.name = "Load SSIDs";
  saveAPsMenu.name = "Save APs";
  loadAPsMenu.name = "Load APs";
  saveATsMenu.name = "Save Airtags";
  loadATsMenu.name = "Load Airtags";

  bluetoothSnifferMenu.name = text_table1[23];
  bluetoothAttackMenu.name = "Bluetooth Attacks";
  generateSSIDsMenu.name = text_table1[27];
  clearSSIDsMenu.name = text_table1[28];
  clearAPsMenu.name = text_table1[29];
  wifiAPMenu.name = "Access Points";
  wifiIPMenu.name = "Active IPs";
  apInfoMenu.name = "AP Info";
  setMacMenu.name = "Set MACs";
  genAPMacMenu.name = "Generate AP MAC";
  #ifdef HAS_BT
    airtagMenu.name = "Select Airtag";
  #endif
  //#ifndef HAS_ILI9341
    wifiStationMenu.name = "Select Stations";
  //#endif
  #ifdef HAS_GPS
    gpsMenu.name = "GPS"; 
    gpsInfoMenu.name = "GPS Data";
    wardrivingMenu.name = "Wardriving";
  #endif  
  htmlMenu.name = "EP HTML List";
  //#if (!defined(HAS_ILI9341) && defined(HAS_BUTTONS))
    miniKbMenu.name = "Mini Keyboard";
  //#endif
  #ifdef HAS_SD
  //  #ifndef HAS_ILI9341
      sdDeleteMenu.name = "Delete SD Files";
  //  #endif
  #endif
  selectProbeSSIDsMenu.name = "Probe Requests";
  evilPortalMenu.name = "Evil Portal";
  ssidsMenu.name = "SSIDs";

  gpsPOIMenu.name = "GPS POI";

  // Build Main Menu
  mainMenu.parentMenu = NULL;
  this->addNodes(&mainMenu, text_table1[7], TFTGREEN, NULL, WIFI, [this]() {
    this->changeMenu(&wifiMenu);
  });
  this->addNodes(&mainMenu, text_table1[19], TFTCYAN, NULL, BLUETOOTH, [this]() {
    this->changeMenu(&bluetoothMenu);
  });
  #ifdef HAS_GPS
    this->addNodes(&mainMenu, text1_66, TFTRED, NULL, GPS_MENU, [this]() {
      this->changeMenu(&gpsMenu);
    });
  #endif
  this->addNodes(&mainMenu, text_table1[9], TFTBLUE, NULL, DEVICE, [this]() {
    this->changeMenu(&deviceMenu);
  });
  this->addNodes(&mainMenu, text_table1[30], TFTLIGHTGREY, NULL, REBOOT, []() {
    ESP.restart();
  });

  // Build WiFi Menu
  wifiMenu.parentMenu = &mainMenu; // Main Menu is second menu parent
  this->addNodes(&wifiMenu, text09, TFTLIGHTGREY, NULL, 0, [this]() {
    this->changeMenu(wifiMenu.parentMenu);
  });
  this->addNodes(&wifiMenu, text_table1[31], TFTYELLOW, NULL, SNIFFERS, [this]() {
    this->changeMenu(&wifiSnifferMenu);
  });
  this->addNodes(&wifiMenu, "Scanners", TFTORANGE, NULL, SCANNERS, [this]() {
    this->changeMenu(&wifiScannerMenu);
  });
  #ifdef HAS_GPS
    this->addNodes(&wifiMenu, "Wardriving", TFTGREEN, NULL, BEACON_SNIFF, [this]() {
      this->changeMenu(&wardrivingMenu);
    });
  #endif
  this->addNodes(&wifiMenu, text_table1[32], TFTRED, NULL, ATTACKS, [this]() {
    this->changeMenu(&wifiAttackMenu);
  });
  this->addNodes(&wifiMenu, text_table1[33], TFTPURPLE, NULL, GENERAL_APPS, [this]() {
    this->changeMenu(&wifiGeneralMenu);
  });

  // Build WiFi scanner Menu
  wifiScannerMenu.parentMenu = &wifiMenu; // Main Menu is second menu parent
  this->addNodes(&wifiScannerMenu, text09, TFTLIGHTGREY, NULL, 0, [this]() {
    this->changeMenu(wifiScannerMenu.parentMenu);
  });
  this->addNodes(&wifiScannerMenu, "Ping Scan", TFTGREEN, NULL, SCANNERS, [this]() {
    display_obj.clearScreen();
    this->drawStatusBar();
    wifi_scan_obj.StartScan(WIFI_PING_SCAN, TFT_CYAN);
  });
  this->addNodes(&wifiScannerMenu, "ARP Scan", TFTCYAN, NULL, SCANNERS, [this]() {
    display_obj.clearScreen();
    this->drawStatusBar();
    wifi_scan_obj.StartScan(WIFI_ARP_SCAN, TFT_CYAN);
  });
  this->addNodes(&wifiScannerMenu, "Port Scan All", TFTMAGENTA, NULL, BEACON_LIST, [this](){
    // Add the back button
    wifiIPMenu.list->clear();
      this->addNodes(&wifiIPMenu, text09, TFTLIGHTGREY, NULL, 0, [this]() {
      this->changeMenu(wifiIPMenu.parentMenu);
    });

    // Populate the menu with buttons
    for (int i = 0; i < ipList->size(); i++) {
      // This is the menu node
      this->addNodes(&wifiIPMenu, ipList->get(i).toString(), TFTBLUE, NULL, 255, [this, i](){
        Serial.println("Selected: " + ipList->get(i).toString());
        wifi_scan_obj.current_scan_ip = ipList->get(i);
        display_obj.clearScreen();
        this->drawStatusBar();
        wifi_scan_obj.StartScan(WIFI_PORT_SCAN_ALL, TFT_BLUE);
      });
    }
    this->changeMenu(&wifiIPMenu);
  });
  this->addNodes(&wifiScannerMenu, "SSH Scan", TFTORANGE, NULL, SCANNERS, [this]() {
    display_obj.clearScreen();
    this->drawStatusBar();
    wifi_scan_obj.StartScan(WIFI_SCAN_SSH, TFT_CYAN);
  });
  this->addNodes(&wifiScannerMenu, "Telnet Scan", TFTRED, NULL, SCANNERS, [this]() {
    display_obj.clearScreen();
    this->drawStatusBar();
    wifi_scan_obj.StartScan(WIFI_SCAN_TELNET, TFT_CYAN);
  });

  // Build WiFi sniffer Menu
  wifiSnifferMenu.parentMenu = &wifiMenu; // Main Menu is second menu parent
  this->addNodes(&wifiSnifferMenu, text09, TFTLIGHTGREY, NULL, 0, [this]() {
    this->changeMenu(wifiSnifferMenu.parentMenu);
  });
  this->addNodes(&wifiSnifferMenu, text_table1[42], TFTCYAN, NULL, PROBE_SNIFF, [this]() {
    display_obj.clearScreen();
    this->drawStatusBar();
    wifi_scan_obj.StartScan(WIFI_SCAN_PROBE, TFT_CYAN);
  });
  this->addNodes(&wifiSnifferMenu, text_table1[43], TFTMAGENTA, NULL, BEACON_SNIFF, [this]() {
    display_obj.clearScreen();
    this->drawStatusBar();
    wifi_scan_obj.StartScan(WIFI_SCAN_AP, TFT_MAGENTA);
  });
  this->addNodes(&wifiSnifferMenu, text_table1[44], TFTRED, NULL, DEAUTH_SNIFF, [this]() {
    display_obj.clearScreen();
    this->drawStatusBar();
    wifi_scan_obj.StartScan(WIFI_SCAN_DEAUTH, TFT_RED);
  });
  this->addNodes(&wifiSnifferMenu, "Packet Count", TFTORANGE, NULL, PACKET_MONITOR, [this]() {
    display_obj.clearScreen();
    this->drawStatusBar();
    wifi_scan_obj.StartScan(WIFI_SCAN_PACKET_RATE, TFT_ORANGE);
    wifi_scan_obj.renderPacketRate();
  });
  #ifdef HAS_ILI9341
    this->addNodes(&wifiSnifferMenu, text_table1[46], TFTVIOLET, NULL, EAPOL, [this]() {
      wifi_scan_obj.StartScan(WIFI_SCAN_EAPOL, TFT_VIOLET);
    });
    this->addNodes(&wifiSnifferMenu, text_table1[45], TFTBLUE, NULL, PACKET_MONITOR, [this]() {
      wifi_scan_obj.StartScan(WIFI_PACKET_MONITOR, TFT_BLUE);
    });
  #else // No touch
    this->addNodes(&wifiSnifferMenu, text_table1[46], TFTVIOLET, NULL, EAPOL, [this]() {
      display_obj.clearScreen();
      this->drawStatusBar();
      wifi_scan_obj.StartScan(WIFI_SCAN_EAPOL, TFT_VIOLET);
    });
    this->addNodes(&wifiSnifferMenu, text_table1[45], TFTBLUE, NULL, PACKET_MONITOR, [this]() {
      display_obj.clearScreen();
      this->drawStatusBar();
      wifi_scan_obj.StartScan(WIFI_PACKET_MONITOR, TFT_BLUE);
    });
    /*this->addNodes(&wifiSnifferMenu, "Packet Count", TFTORANGE, NULL, PACKET_MONITOR, [this]() {
      display_obj.clearScreen();
      this->drawStatusBar();
      wifi_scan_obj.StartScan(WIFI_SCAN_PACKET_RATE, TFT_ORANGE);
      wifi_scan_obj.renderPacketRate();
    });*/
  #endif
  this->addNodes(&wifiSnifferMenu, "Channel Analyzer", TFTCYAN, NULL, PACKET_MONITOR, [this]() {
    display_obj.clearScreen();
    this->drawStatusBar();
    this->renderGraphUI(WIFI_SCAN_CHAN_ANALYZER);
    wifi_scan_obj.StartScan(WIFI_SCAN_CHAN_ANALYZER, TFT_CYAN);
  });

  this->addNodes(&wifiSnifferMenu, text_table1[58], TFTWHITE, NULL, PACKET_MONITOR, [this]() {
    display_obj.clearScreen();
    this->drawStatusBar();
    wifi_scan_obj.StartScan(WIFI_SCAN_RAW_CAPTURE, TFT_WHITE);
  });

  this->addNodes(&wifiSnifferMenu, text_table1[47], TFTRED, NULL, PWNAGOTCHI, [this]() {
    display_obj.clearScreen();
    this->drawStatusBar();
    wifi_scan_obj.StartScan(WIFI_SCAN_PWN, TFT_RED);
  });
  
  this->addNodes(&wifiSnifferMenu, text_table1[63], TFTYELLOW, NULL, PINESCAN_SNIFF, [this]() {
    display_obj.clearScreen();
    this->drawStatusBar();
    wifi_scan_obj.StartScan(WIFI_SCAN_PINESCAN, TFT_YELLOW);
  });

  this->addNodes(&wifiSnifferMenu, text_table1[64], TFTORANGE, NULL, MULTISSID_SNIFF, [this]() {
    display_obj.clearScreen();
    this->drawStatusBar();
    wifi_scan_obj.StartScan(WIFI_SCAN_MULTISSID, TFT_ORANGE);
  });
  //#ifndef HAS_ILI9341
    this->addNodes(&wifiSnifferMenu, text_table1[49], TFTMAGENTA, NULL, BEACON_SNIFF, [this]() {
      display_obj.clearScreen();
      this->drawStatusBar();
      wifi_scan_obj.StartScan(WIFI_SCAN_TARGET_AP, TFT_MAGENTA);
    });
  //#endif
  this->addNodes(&wifiSnifferMenu, "Scan All", TFTLIME, NULL, BEACON_SNIFF, [this]() {
    display_obj.clearScreen();
    this->drawStatusBar();
    wifi_scan_obj.StartScan(WIFI_SCAN_AP_STA, 0x97e0);
  });
  //#ifndef HAS_ILI9341
    this->addNodes(&wifiSnifferMenu, text_table1[59], TFTORANGE, NULL, PACKET_MONITOR, [this]() {
      display_obj.clearScreen();
      this->drawStatusBar();
      wifi_scan_obj.StartScan(WIFI_SCAN_STATION, TFT_WHITE);
    });
  //#endif
  //#ifdef HAS_ILI9341
  this->addNodes(&wifiSnifferMenu, "Signal Monitor", TFTCYAN, NULL, PACKET_MONITOR, [this]() {
    display_obj.clearScreen();
    this->drawStatusBar();
    wifi_scan_obj.StartScan(WIFI_SCAN_SIG_STREN, TFT_CYAN);
  });
  //#endif

  // Build Wardriving menu
  #ifdef HAS_GPS
    wardrivingMenu.parentMenu = &wifiMenu; // Main Menu is second menu parent
    this->addNodes(&wardrivingMenu, text09, TFTLIGHTGREY, NULL, 0, [this]() {
      this->changeMenu(wardrivingMenu.parentMenu);
    });
    if (gps_obj.getGpsModuleStatus()) {
      this->addNodes(&wardrivingMenu, "Wardrive", TFTGREEN, NULL, BEACON_SNIFF, [this]() {
        display_obj.clearScreen();
        this->drawStatusBar();
        wifi_scan_obj.StartScan(WIFI_SCAN_WAR_DRIVE, TFT_GREEN);
      });
    }
  #endif
  #ifdef HAS_GPS
    if (gps_obj.getGpsModuleStatus()) {
      this->addNodes(&wardrivingMenu, "Station Wardrive", TFTORANGE, NULL, PROBE_SNIFF, [this]() {
        display_obj.clearScreen();
        this->drawStatusBar();
        wifi_scan_obj.StartScan(WIFI_SCAN_STATION_WAR_DRIVE, TFT_ORANGE);
      });
    }
  #endif

  // Build WiFi attack menu
  wifiAttackMenu.parentMenu = &wifiMenu; // Main Menu is second menu parent
  this->addNodes(&wifiAttackMenu, text09, TFTLIGHTGREY, NULL, 0, [this]() {
    this->changeMenu(wifiAttackMenu.parentMenu);
  });
  this->addNodes(&wifiAttackMenu, text_table1[50], TFTRED, NULL, BEACON_LIST, [this]() {
    display_obj.clearScreen();
    this->drawStatusBar();
    wifi_scan_obj.StartScan(WIFI_ATTACK_BEACON_LIST, TFT_RED);
  });
  this->addNodes(&wifiAttackMenu, text_table1[51], TFTORANGE, NULL, BEACON_SPAM, [this]() {
    display_obj.clearScreen();
    this->drawStatusBar();
    wifi_scan_obj.StartScan(WIFI_ATTACK_BEACON_SPAM, TFT_ORANGE);
  });
  this->addNodes(&wifiAttackMenu, text_table1[52], TFTYELLOW, NULL, RICK_ROLL, [this]() {
    display_obj.clearScreen();
    this->drawStatusBar();
    wifi_scan_obj.StartScan(WIFI_ATTACK_RICK_ROLL, TFT_YELLOW);
  });
  this->addNodes(&wifiAttackMenu, text_table1[53], TFTRED, NULL, PROBE_SNIFF, [this]() {
    display_obj.clearScreen();
    this->drawStatusBar();
    wifi_scan_obj.StartScan(WIFI_ATTACK_AUTH, TFT_RED);
  });
  /*this->addNodes(&wifiAttackMenu, "Evil Portal", TFTORANGE, NULL, BEACON_SNIFF, [this]() {
    display_obj.clearScreen();
    this->drawStatusBar();
    wifi_scan_obj.StartScan(WIFI_SCAN_EVIL_PORTAL, TFT_ORANGE);
    wifi_scan_obj.setMac();
  });*/
  this->addNodes(&wifiAttackMenu, "Evil Portal", TFTORANGE, NULL, BEACON_SNIFF, [this]() {

    wifiAPMenu.list->clear();
    ssidsMenu.list->clear();

    wifiAPMenu.parentMenu = &evilPortalMenu;
    ssidsMenu.parentMenu = &evilPortalMenu;

    this->addNodes(&wifiAPMenu, text09, TFTLIGHTGREY, NULL, 0, [this]() {
      this->changeMenu(wifiAPMenu.parentMenu);
    });
    this->addNodes(&ssidsMenu, text09, TFTLIGHTGREY, NULL, 0, [this]() {
      this->changeMenu(ssidsMenu.parentMenu);
    });

    // Get AP list ready
    for (int i = 0; i < access_points->size(); i++) {
      // This is the menu node
      this->addNodes(&wifiAPMenu, access_points->get(i).essid, TFTCYAN, NULL, 255, [this, i](){
        if (evil_portal_obj.setAP(access_points->get(i).essid)) {
          AccessPoint new_ap = access_points->get(i);
          new_ap.selected = true;
          access_points->set(i, new_ap);

          evil_portal_obj.ap_index = i;

          display_obj.clearScreen();
          this->drawStatusBar();
          wifi_scan_obj.StartScan(WIFI_SCAN_EVIL_PORTAL, TFT_ORANGE);
          wifi_scan_obj.setMac();
        }
        else
          this->changeMenu(&evilPortalMenu);
      });
    }

    for (int i = 0; i < ssids->size(); i++) {
      // This is the menu node
      this->addNodes(&ssidsMenu, ssids->get(i).essid, TFTCYAN, NULL, 255, [this, i](){
        if (evil_portal_obj.setAP(ssids->get(i).essid)) {
          display_obj.clearScreen();
          this->drawStatusBar();
          wifi_scan_obj.StartScan(WIFI_SCAN_EVIL_PORTAL, TFT_ORANGE);
          wifi_scan_obj.setMac();
        }
        else
          this->changeMenu(&evilPortalMenu);
      });
    }
    this->changeMenu(&evilPortalMenu);
  });
  this->addNodes(&wifiAttackMenu, text_table1[54], TFTRED, NULL, DEAUTH_SNIFF, [this]() {
    display_obj.clearScreen();
    this->drawStatusBar();
    wifi_scan_obj.StartScan(WIFI_ATTACK_DEAUTH, TFT_RED);
  });
  this->addNodes(&wifiAttackMenu, text_table1[57], TFTMAGENTA, NULL, BEACON_LIST, [this]() {
    display_obj.clearScreen();
    this->drawStatusBar();
    wifi_scan_obj.StartScan(WIFI_ATTACK_AP_SPAM, TFT_MAGENTA);
  });
  this->addNodes(&wifiAttackMenu, text_table1[62], TFTRED, NULL, DEAUTH_SNIFF, [this]() {
    display_obj.clearScreen();
    this->drawStatusBar();
    wifi_scan_obj.StartScan(WIFI_ATTACK_DEAUTH_TARGETED, TFT_ORANGE);
  });

  this->addNodes(&wifiAttackMenu, "Karma", TFTORANGE, NULL, KEYBOARD_ICO, [this](){
    // Add the back button
    selectProbeSSIDsMenu.list->clear();
    this->addNodes(&selectProbeSSIDsMenu, text09, TFTLIGHTGREY, NULL, 0, [this]() {
      this->changeMenu(&wifiAttackMenu);
    });

    // Populate the menu with buttons
    for (int i = 0; i < probe_req_ssids->size(); i++) {
      // This is the menu node
      this->addNodes(&selectProbeSSIDsMenu, probe_req_ssids->get(i).essid, TFTCYAN, NULL, 255, [this, i](){
        if (evil_portal_obj.setAP(probe_req_ssids->get(i).essid)) {
          display_obj.clearScreen();
          this->drawStatusBar();
          wifi_scan_obj.StartScan(WIFI_SCAN_EVIL_PORTAL, TFT_ORANGE);
          wifi_scan_obj.setMac();
        }
        else
          this->changeMenu(&wifiAttackMenu);
      });
    }
    this->changeMenu(&selectProbeSSIDsMenu);
  });

  this->addNodes(&wifiAttackMenu, "Bad Msg", TFTRED, NULL, DEAUTH_SNIFF, [this]() {
    display_obj.clearScreen();
    this->drawStatusBar();
    wifi_scan_obj.StartScan(WIFI_ATTACK_BAD_MSG, TFT_RED);
  });
  this->addNodes(&wifiAttackMenu, "Bad Msg Targeted", TFTYELLOW, NULL, DEAUTH_SNIFF, [this]() {
    display_obj.clearScreen();
    this->drawStatusBar();
    wifi_scan_obj.StartScan(WIFI_ATTACK_BAD_MSG_TARGETED, TFT_YELLOW);
  });
  this->addNodes(&wifiAttackMenu, "Assoc Sleep", TFTRED, NULL, DEAUTH_SNIFF, [this]() {
    display_obj.clearScreen();
    this->drawStatusBar();
    wifi_scan_obj.StartScan(WIFI_ATTACK_SLEEP, TFT_RED);
  });
  this->addNodes(&wifiAttackMenu, "Assoc Sleep Targ", TFTMAGENTA, NULL, DEAUTH_SNIFF, [this]() {
    display_obj.clearScreen();
    this->drawStatusBar();
    wifi_scan_obj.StartScan(WIFI_ATTACK_SLEEP_TARGETED, TFT_MAGENTA);
  });

  evilPortalMenu.parentMenu = &wifiAttackMenu;
  this->addNodes(&evilPortalMenu, text09, TFTLIGHTGREY, NULL, 0, [this]() {
    this->changeMenu(evilPortalMenu.parentMenu);
  });
  this->addNodes(&evilPortalMenu, "Access Points", TFTGREEN, NULL, BEACON_SNIFF, [this]() {
    this->changeMenu(&wifiAPMenu);
  });
  this->addNodes(&evilPortalMenu, "User SSIDs", TFTCYAN, NULL, PROBE_SNIFF, [this]() {
    this->changeMenu(&ssidsMenu);
  });

  // Build WiFi General menu
  wifiGeneralMenu.parentMenu = &wifiMenu;
  this->addNodes(&wifiGeneralMenu, text09, TFTLIGHTGREY, NULL, 0, [this]() {
    this->changeMenu(wifiGeneralMenu.parentMenu);
  });
  this->addNodes(&wifiGeneralMenu, text_table1[27], TFTSKYBLUE, NULL, GENERATE, [this]() {
    this->changeMenu(&generateSSIDsMenu);
    wifi_scan_obj.RunGenerateSSIDs();
  });

	//Add Select probe ssid
  this->addNodes(&wifiGeneralMenu, text_table1[65], TFTCYAN, NULL, KEYBOARD_ICO, [this]() {
    selectProbeSSIDsMenu.list->clear();

    // Add the back button
    this->addNodes(&selectProbeSSIDsMenu, text09, TFTLIGHTGREY, NULL, 0, [this]() {
      this->changeMenu(&wifiGeneralMenu);

      // TODO: TBD - Should probe_req_ssids have it´s own life and override ap.config and/or ssids -list for EP?
      // If so, then we should not add selected ssids to ssids list

      // Add selected ssid names to ssids list when clicking back button
      if (probe_req_ssids->size() > 0) {

        //TODO: TBD - Clear ssids list before adding new ones??

        for (int i = 0; i < probe_req_ssids->size(); i++) {
          ProbeReqSsid cur_probe_ssid = probe_req_ssids->get(i);
          if (cur_probe_ssid.selected) {
            bool ssidExists = false;
            for (int i = 0; i < ssids->size(); i++) {
              if (ssids->get(i).essid == cur_probe_ssid.essid) {
                ssidExists = true;
                break;
              }
            }
            if (!ssidExists) {
              wifi_scan_obj.addSSID(cur_probe_ssid.essid);
            }
          }
        }
      }
    });

    // Populate the menu with buttons
    for (int i = 0; i < probe_req_ssids->size(); i++) {
      ProbeReqSsid cur_ssid = probe_req_ssids->get(i);
      // This is the menu node
      this->addNodes(
        &selectProbeSSIDsMenu,
        "[" + String(cur_ssid.requests) + "]" + cur_ssid.essid,
        TFTCYAN,
        NULL,
        255,
        [this, i]() {
          ProbeReqSsid new_ssid = probe_req_ssids->get(i);
          new_ssid.selected = !probe_req_ssids->get(i).selected;

          // Change selection status of menu node
          MenuNode new_node = current_menu->list->get(i + 1);
          new_node.selected = !current_menu->list->get(i + 1).selected;
          current_menu->list->set(i + 1, new_node);

          probe_req_ssids->set(i, new_ssid);
        },
        probe_req_ssids->get(i).selected);
    }
    this->changeMenu(&selectProbeSSIDsMenu);
  });

  #ifdef HAS_ILI9341
    this->addNodes(&wifiGeneralMenu, text_table1[1], TFTNAVY, NULL, KEYBOARD_ICO, [this](){
      display_obj.clearScreen(); 
      wifi_scan_obj.StartScan(LV_ADD_SSID, TFT_YELLOW); 
      addSSIDGFX();
    });
  #endif
  #if (!defined(HAS_ILI9341) && defined(HAS_BUTTONS))
    this->addNodes(&wifiGeneralMenu, text_table1[1], TFTNAVY, NULL, KEYBOARD_ICO, [this](){
      this->changeMenu(&miniKbMenu);
      this->miniKeyboard(&miniKbMenu);
    });
  #endif
  this->addNodes(&wifiGeneralMenu, text_table1[28], TFTSILVER, NULL, CLEAR_ICO, [this]() {
    this->changeMenu(&clearSSIDsMenu);
    wifi_scan_obj.RunClearSSIDs();
  });
  this->addNodes(&wifiGeneralMenu, text_table1[29], TFTDARKGREY, NULL, CLEAR_ICO, [this]() {
    this->changeMenu(&clearAPsMenu);
    wifi_scan_obj.RunClearAPs();
  });
  this->addNodes(&wifiGeneralMenu, text_table1[60], TFTBLUE, NULL, CLEAR_ICO, [this]() {
    this->changeMenu(&clearAPsMenu);
    wifi_scan_obj.RunClearStations();
  });
  /*#ifdef HAS_ILI9341
    // Select APs on OG
    this->addNodes(&wifiGeneralMenu, text_table1[56], TFTNAVY, NULL, KEYBOARD_ICO, [this](){
      display_obj.clearScreen(); 
      wifi_scan_obj.currentScanMode = LV_ADD_SSID; 
      wifi_scan_obj.StartScan(LV_ADD_SSID, TFT_RED);  
      addAPGFX();
    });
    // Select Stations on OG
    this->addNodes(&wifiGeneralMenu, text_table1[61], TFTLIGHTGREY, NULL, KEYBOARD_ICO, [this](){
      display_obj.clearScreen(); 
      wifi_scan_obj.currentScanMode = LV_ADD_SSID; 
      wifi_scan_obj.StartScan(LV_ADD_SSID, TFT_RED);  
      addStationGFX();
    });
    // Select Evil Portal Files on OG
    this->addNodes(&wifiGeneralMenu, "Select EP HTML File", TFTCYAN, NULL, KEYBOARD_ICO, [this](){
      display_obj.clearScreen(); 
      wifi_scan_obj.currentScanMode = LV_ADD_SSID; 
      wifi_scan_obj.StartScan(LV_ADD_SSID, TFT_RED);  
      selectEPHTMLGFX();
    });
    apInfoMenu.parentMenu = &wifiGeneralMenu;
    this->addNodes(&apInfoMenu, text09, TFTLIGHTGREY, NULL, 0, [this]() {
      this->changeMenu(apInfoMenu.parentMenu);
    });*/
  //#else // Mini EP HTML select
    this->addNodes(&wifiGeneralMenu, "Select EP HTML File", TFTCYAN, NULL, KEYBOARD_ICO, [this](){
      // Add the back button
      htmlMenu.list->clear();
        this->addNodes(&htmlMenu, text09, TFTLIGHTGREY, NULL, 0, [this]() {
        this->changeMenu(htmlMenu.parentMenu);
      });

      // Populate the menu with buttons
      for (int i = 0; i < evil_portal_obj.html_files->size(); i++) {
        // This is the menu node
        this->addNodes(&htmlMenu, evil_portal_obj.html_files->get(i), TFTCYAN, NULL, 255, [this, i](){
          evil_portal_obj.selected_html_index = i;
          evil_portal_obj.target_html_name = evil_portal_obj.html_files->get(evil_portal_obj.selected_html_index);
          Serial.println("Set Evil Portal HTML as " + evil_portal_obj.target_html_name);
          evil_portal_obj.using_serial_html = false;
          this->changeMenu(htmlMenu.parentMenu);
          return;
        });
      }
      this->changeMenu(&htmlMenu);
    });

    //#if (!defined(HAS_ILI9341) && defined(HAS_BUTTONS))
      miniKbMenu.parentMenu = &wifiGeneralMenu;
      #ifndef MARAUDER_CARDPUTER
        this->addNodes(&miniKbMenu, "a", TFTCYAN, NULL, 0, [this]() {
          this->changeMenu(miniKbMenu.parentMenu);
        });
      #endif
    //#endif

    htmlMenu.parentMenu = &wifiGeneralMenu;
    this->addNodes(&htmlMenu, text09, TFTLIGHTGREY, NULL, 0, [this]() {
      this->changeMenu(htmlMenu.parentMenu);
    });

    // Select APs on Mini
    this->addNodes(&wifiGeneralMenu, "Select APs", TFTNAVY, NULL, KEYBOARD_ICO, [this](){
      wifiAPMenu.parentMenu = &wifiGeneralMenu;
      // Add the back button
      wifiAPMenu.list->clear();
        this->addNodes(&wifiAPMenu, text09, TFTLIGHTGREY, NULL, 0, [this]() {
        this->changeMenu(wifiAPMenu.parentMenu);
      });

      this->addNodes(&wifiAPMenu, "Select ALL", TFTGREEN, NULL, 255, [this](){

        for (int x = 0; x < access_points->size(); x++) {
          AccessPoint new_ap = access_points->get(x);
          new_ap.selected = !access_points->get(x).selected;
          access_points->set(x, new_ap);

          MenuNode new_node = current_menu->list->get(x + 2);
          new_node.selected = !current_menu->list->get(x + 2).selected;
          current_menu->list->set(x + 2, new_node);
        }

        this->changeMenu(current_menu);

      });

      // Populate the menu with buttons
      for (int i = 0; i < access_points->size(); i++) {
        // This is the menu node
        this->addNodes(&wifiAPMenu, access_points->get(i).essid, TFTCYAN, NULL, 255, [this, i](){
        AccessPoint new_ap = access_points->get(i);
        new_ap.selected = !access_points->get(i).selected;

        // Change selection status of menu node
        MenuNode new_node = current_menu->list->get(i + 2);
        new_node.selected = !current_menu->list->get(i + 2).selected;
        current_menu->list->set(i + 2, new_node);

        access_points->set(i, new_ap);
        }, access_points->get(i).selected);
      }
      this->changeMenu(&wifiAPMenu);
    });

    this->addNodes(&wifiGeneralMenu, "View AP Info", TFTCYAN, NULL, KEYBOARD_ICO, [this](){
      // Add the back button
      wifiAPMenu.list->clear();
        this->addNodes(&wifiAPMenu, text09, TFTLIGHTGREY, NULL, 0, [this]() {
        this->changeMenu(wifiAPMenu.parentMenu);
      });

      // Populate the menu with buttons
      for (int i = 0; i < access_points->size(); i++) {
        // This is the menu node
        this->addNodes(&wifiAPMenu, access_points->get(i).essid, TFTCYAN, NULL, 255, [this, i](){
          this->changeMenu(&apInfoMenu);
          wifi_scan_obj.RunAPInfo(i);
        });
      }
      this->changeMenu(&wifiAPMenu);
    });

    apInfoMenu.parentMenu = &wifiAPMenu;
    this->addNodes(&apInfoMenu, text09, TFTLIGHTGREY, NULL, 0, [this]() {
      this->changeMenu(apInfoMenu.parentMenu);
    });

    wifiAPMenu.parentMenu = &wifiGeneralMenu;
    this->addNodes(&wifiAPMenu, text09, TFTLIGHTGREY, NULL, 0, [this]() {
      this->changeMenu(wifiAPMenu.parentMenu);
    });

    wifiIPMenu.parentMenu = &wifiScannerMenu;
    this->addNodes(&wifiIPMenu, text09, TFTLIGHTGREY, NULL, 0, [this]() {
      this->changeMenu(wifiIPMenu.parentMenu);
    });


    // Select Stations on Mini v2
    this->addNodes(&wifiGeneralMenu, "Select Stations", TFTCYAN, NULL, KEYBOARD_ICO, [this](){
      wifiAPMenu.list->clear();
        this->addNodes(&wifiAPMenu, text09, TFTLIGHTGREY, NULL, 0, [this]() {
        this->changeMenu(wifiAPMenu.parentMenu);
      });

      int menu_limit = access_points->size();


      for (int i = 0; i < menu_limit; i++) {
        wifiStationMenu.list->clear();
        this->addNodes(&wifiAPMenu, access_points->get(i).essid, TFTCYAN, NULL, 255, [this, i](){

          wifiStationMenu.list->clear();

          // Add back button to the APs
          this->addNodes(&wifiStationMenu, text09, TFTLIGHTGREY, NULL, 0, [this]() {
            this->changeMenu(wifiStationMenu.parentMenu);
          });

          this->addNodes(&wifiStationMenu, "Select ALL", TFTGREEN, NULL, 255, [this, i](){

            for (int y = 0; y < access_points->get(i).stations->size(); y++) {
              int cur_ap_sta_inx = access_points->get(i).stations->get(y);
              Station new_sta = stations->get(cur_ap_sta_inx);
              new_sta.selected = !stations->get(cur_ap_sta_inx).selected;

              // Change selection status of menu node
              MenuNode new_node = current_menu->list->get(y + 2);
              new_node.selected = !current_menu->list->get(y + 2).selected;
              current_menu->list->set(y + 2, new_node);

              stations->set(cur_ap_sta_inx, new_sta);
            }

            this->changeMenu(current_menu);

          });

          // Add the AP's stations to the specific AP menu
          for (int x = 0; x < access_points->get(i).stations->size(); x++) {
            int cur_ap_sta = access_points->get(i).stations->get(x);

            this->addNodes(&wifiStationMenu, macToString(stations->get(cur_ap_sta)), TFTCYAN, NULL, 255, [this, i, cur_ap_sta, x](){
            Station new_sta = stations->get(cur_ap_sta);
            new_sta.selected = !stations->get(cur_ap_sta).selected;

            // Change selection status of menu node
            MenuNode new_node = current_menu->list->get(x + 2);
            new_node.selected = !current_menu->list->get(x + 2).selected;
            current_menu->list->set(x + 2, new_node);

            stations->set(cur_ap_sta, new_sta);
            }, stations->get(cur_ap_sta).selected);
          }

          // Final change menu to the menu of Stations
          this->changeMenu(&wifiStationMenu);
          
        }, false);
      }
      this->changeMenu(&wifiAPMenu);
    });

    this->addNodes(&wifiGeneralMenu, "Join WiFi", TFTWHITE, NULL, KEYBOARD_ICO, [this](){
      // Add the back button
      wifiAPMenu.list->clear();
        this->addNodes(&wifiAPMenu, text09, TFTLIGHTGREY, NULL, 0, [this]() {
        this->changeMenu(wifiAPMenu.parentMenu);
      });

      // Populate the menu with buttons
      for (int i = 0; i < access_points->size(); i++) {
        // This is the menu node
        this->addNodes(&wifiAPMenu, access_points->get(i).essid, TFTCYAN, NULL, 255, [this, i](){
          // Join WiFi using mini keyboard
          #ifdef HAS_MINI_KB
            this->changeMenu(&miniKbMenu);
            String password = this->miniKeyboard(&miniKbMenu, true);
            if (password != "") {
              Serial.println("Using SSID: " + (String)access_points->get(i).essid + " Password: " + (String)password);
              wifi_scan_obj.currentScanMode = LV_JOIN_WIFI;
              wifi_scan_obj.StartScan(LV_JOIN_WIFI, TFT_YELLOW); 
              wifi_scan_obj.joinWiFi(access_points->get(i).essid, password);
              this->changeMenu(current_menu);
            }
          #endif

          // Join WiFi using touch screen keyboard
          #ifdef HAS_TOUCH
            wifi_scan_obj.currentScanMode = LV_JOIN_WIFI;
            wifi_scan_obj.StartScan(LV_JOIN_WIFI, TFT_YELLOW); 
            joinWiFiGFX(access_points->get(i).essid);
          #endif
        });
      }
      this->changeMenu(&wifiAPMenu);
    });

    this->addNodes(&wifiGeneralMenu, "Join Saved WiFi", TFTWHITE, NULL, KEYBOARD_ICO, [this](){
      String ssid = settings_obj.loadSetting<String>("ClientSSID");
      String pw = settings_obj.loadSetting<String>("ClientPW");

      if ((ssid != "") && (pw != "")) {
        wifi_scan_obj.joinWiFi(ssid, pw, false);
        this->changeMenu(&wifiGeneralMenu);
      }
      else {
        // Add the back button
        wifiAPMenu.list->clear();
          this->addNodes(&wifiAPMenu, text09, TFTLIGHTGREY, NULL, 0, [this]() {
          this->changeMenu(wifiAPMenu.parentMenu);
        });

        // Populate the menu with buttons
        for (int i = 0; i < access_points->size(); i++) {
          // This is the menu node
          this->addNodes(&wifiAPMenu, access_points->get(i).essid, TFTCYAN, NULL, 255, [this, i](){
            // Join WiFi using mini keyboard
            #ifdef HAS_MINI_KB
              this->changeMenu(&miniKbMenu);
              String password = this->miniKeyboard(&miniKbMenu, true);
              if (password != "") {
                Serial.println("Using SSID: " + (String)access_points->get(i).essid + " Password: " + (String)password);
                wifi_scan_obj.currentScanMode = LV_JOIN_WIFI;
                wifi_scan_obj.StartScan(LV_JOIN_WIFI, TFT_YELLOW); 
                wifi_scan_obj.joinWiFi(access_points->get(i).essid, password);
                this->changeMenu(current_menu);
              }
            #endif

            // Join WiFi using touch screen keyboard
            #ifdef HAS_TOUCH
              wifi_scan_obj.currentScanMode = LV_JOIN_WIFI;
              wifi_scan_obj.StartScan(LV_JOIN_WIFI, TFT_YELLOW); 
              joinWiFiGFX(access_points->get(i).essid);
            #endif
          });
        }
        this->changeMenu(&wifiAPMenu);
      }
    });

    wifiStationMenu.parentMenu = &wifiAPMenu;
    this->addNodes(&wifiStationMenu, text09, TFTLIGHTGREY, NULL, 0, [this]() {
      this->changeMenu(wifiStationMenu.parentMenu);
    });
  //#endif

  //#ifdef HAS_ILI9341
  //  this->addNodes(&wifiGeneralMenu, "View AP Info", TFTLIGHTGREY, NULL, 0, [this]() {
  //    display_obj.clearScreen();
  //    wifi_scan_obj.currentScanMode = LV_ADD_SSID;
  //    wifi_scan_obj.StartScan(LV_ADD_SSID, TFT_WHITE);
  //    addAPGFX("AP Info");
  //  });
  //#endif

  this->addNodes(&wifiGeneralMenu, "Set MACs", TFTLIGHTGREY, NULL, 0, [this]() {
    this->changeMenu(&setMacMenu);
  });

  this->addNodes(&wifiGeneralMenu, "Shutdown WiFi", TFTRED, NULL, 0, [this]() {
    WiFi.disconnect(true);
    delay(100);
    wifi_scan_obj.StartScan(WIFI_SCAN_OFF, TFT_RED);
    this->changeMenu(current_menu);
  });


  // Menu for generating and setting MAC addrs for AP and STA
  setMacMenu.parentMenu = &wifiGeneralMenu;
  this->addNodes(&setMacMenu, text09, TFTLIGHTGREY, NULL, 0, [this]() {
    this->changeMenu(setMacMenu.parentMenu);
  });

  // Generate random MAC for AP
  this->addNodes(&setMacMenu, "Generate AP MAC", TFTLIME, NULL, 0, [this]() {
    this->changeMenu(&genAPMacMenu);
    wifi_scan_obj.RunGenerateRandomMac(true);
  });

  // Generate random MAC for AP
  this->addNodes(&setMacMenu, "Generate STA MAC", TFTCYAN, NULL, 0, [this]() {
    this->changeMenu(&genAPMacMenu);
    wifi_scan_obj.RunGenerateRandomMac(false);
  });

  // Clone AP MAC to ESP32 for button folks
  //#ifndef HAS_ILI9341
    this->addNodes(&setMacMenu, "Clone AP MAC", TFTRED, NULL, CLEAR_ICO, [this](){
      // Add the back button
      wifiAPMenu.list->clear();
        this->addNodes(&wifiAPMenu, text09, TFTLIGHTGREY, NULL, 0, [this]() {
        this->changeMenu(wifiAPMenu.parentMenu);
      });

      // Populate the menu with buttons
      for (int i = 0; i < access_points->size(); i++) {
        // This is the menu node
        this->addNodes(&wifiAPMenu, access_points->get(i).essid, TFTLIME, NULL, 255, [this, i](){
          this->changeMenu(&genAPMacMenu);
          wifi_scan_obj.RunSetMac(access_points->get(i).bssid, true);
        });
      }
      this->changeMenu(&wifiAPMenu);
    });

    this->addNodes(&setMacMenu, "Clone STA MAC", TFTMAGENTA, NULL, CLEAR_ICO, [this](){
      // Add the back button
      wifiAPMenu.list->clear();
        this->addNodes(&wifiAPMenu, text09, TFTLIGHTGREY, NULL, 0, [this]() {
        this->changeMenu(wifiAPMenu.parentMenu);
      });

      // Populate the menu with buttons
      for (int i = 0; i < stations->size(); i++) {
        // This is the menu node
        this->addNodes(&wifiAPMenu, macToString(stations->get(i).mac), TFTMAGENTA, NULL, 255, [this, i](){
          this->changeMenu(&genAPMacMenu);
          wifi_scan_obj.RunSetMac(stations->get(i).mac, false);
        });
      }
      this->changeMenu(&wifiAPMenu);
    });
  //#endif

  // Menu for generating and setting access point MAC (just goes bacK)
  genAPMacMenu.parentMenu = &wifiGeneralMenu;
  this->addNodes(&genAPMacMenu, text09, TFTLIGHTGREY, NULL, 0, [this]() {
    this->changeMenu(genAPMacMenu.parentMenu);
  });

  // Build generate ssids menu
  generateSSIDsMenu.parentMenu = &wifiGeneralMenu;
  this->addNodes(&generateSSIDsMenu, text09, TFTLIGHTGREY, NULL, 0, [this]() {
    this->changeMenu(generateSSIDsMenu.parentMenu);
  });

  // Build clear ssids menu
  clearSSIDsMenu.parentMenu = &wifiGeneralMenu;
  this->addNodes(&clearSSIDsMenu, text09, TFTLIGHTGREY, NULL, 0, [this]() {
    this->changeMenu(clearSSIDsMenu.parentMenu);
  });
  clearAPsMenu.parentMenu = &wifiGeneralMenu;
  this->addNodes(&clearAPsMenu, text09, TFTLIGHTGREY, NULL, 0, [this]() {
    this->changeMenu(clearAPsMenu.parentMenu);
  });

  // Build Bluetooth Menu
  bluetoothMenu.parentMenu = &mainMenu; // Second Menu is third menu parent
  this->addNodes(&bluetoothMenu, text09, TFTLIGHTGREY, NULL, 0, [this]() {
    this->changeMenu(bluetoothMenu.parentMenu);
  });
  this->addNodes(&bluetoothMenu, text_table1[31], TFTYELLOW, NULL, SNIFFERS, [this]() {
    this->changeMenu(&bluetoothSnifferMenu);
  });
  this->addNodes(&bluetoothMenu, "Bluetooth Attacks", TFTRED, NULL, ATTACKS, [this]() {
    this->changeMenu(&bluetoothAttackMenu);
  });

  // Build bluetooth sniffer Menu
  bluetoothSnifferMenu.parentMenu = &bluetoothMenu; // Second Menu is third menu parent
  this->addNodes(&bluetoothSnifferMenu, text09, TFTLIGHTGREY, NULL, 0, [this]() {
    this->changeMenu(bluetoothSnifferMenu.parentMenu);
  });
  this->addNodes(&bluetoothSnifferMenu, text_table1[34], TFTGREEN, NULL, BLUETOOTH_SNIFF, [this]() {
    display_obj.clearScreen();
    this->drawStatusBar();
    wifi_scan_obj.StartScan(BT_SCAN_ALL, TFT_GREEN);
  });
  this->addNodes(&bluetoothSnifferMenu, "Flipper Sniff", TFTORANGE, NULL, FLIPPER, [this]() {
    display_obj.clearScreen();
    this->drawStatusBar();
    wifi_scan_obj.StartScan(BT_SCAN_FLIPPER, TFT_ORANGE);
  });
  this->addNodes(&bluetoothSnifferMenu, "Airtag Sniff", TFTWHITE, NULL, BLUETOOTH_SNIFF, [this]() {
    display_obj.clearScreen();
    this->drawStatusBar();
    wifi_scan_obj.StartScan(BT_SCAN_AIRTAG, TFT_WHITE);
  });
  #ifdef HAS_GPS
    if (gps_obj.getGpsModuleStatus()) {
      this->addNodes(&bluetoothSnifferMenu, "BT Wardrive", TFTCYAN, NULL, BLUETOOTH_SNIFF, [this]() {
        display_obj.clearScreen();
        this->drawStatusBar();
        wifi_scan_obj.StartScan(BT_SCAN_WAR_DRIVE, TFT_GREEN);
      });
      this->addNodes(&bluetoothSnifferMenu, "BT Wardrive Continuous", TFTRED, NULL, REBOOT, [this]() {
        display_obj.clearScreen();
        this->drawStatusBar();
        wifi_scan_obj.StartScan(BT_SCAN_WAR_DRIVE_CONT, TFT_GREEN);
      });
    }
  #endif
  this->addNodes(&bluetoothSnifferMenu, text_table1[35], TFTMAGENTA, NULL, CC_SKIMMERS, [this]() {
    display_obj.clearScreen();
    this->drawStatusBar();
    wifi_scan_obj.StartScan(BT_SCAN_SKIMMERS, TFT_MAGENTA);
  });
  this->addNodes(&bluetoothSnifferMenu, "Bluetooth Analyzer", TFTCYAN, NULL, PACKET_MONITOR, [this]() {
    display_obj.clearScreen();
    this->drawStatusBar();
    this->renderGraphUI(BT_SCAN_ANALYZER);
    wifi_scan_obj.StartScan(BT_SCAN_ANALYZER, TFT_CYAN);
  });

  // Bluetooth Attack menu
  bluetoothAttackMenu.parentMenu = &bluetoothMenu; // Second Menu is third menu parent
  this->addNodes(&bluetoothAttackMenu, text09, TFTLIGHTGREY, NULL, 0, [this]() {
    this->changeMenu(bluetoothAttackMenu.parentMenu);
  });
  this->addNodes(&bluetoothAttackMenu, "Sour Apple", TFTGREEN, NULL, DEAUTH_SNIFF, [this]() {
    display_obj.clearScreen();
    this->drawStatusBar();
    wifi_scan_obj.StartScan(BT_ATTACK_SOUR_APPLE, TFT_GREEN);
  });
  this->addNodes(&bluetoothAttackMenu, "Swiftpair Spam", TFTCYAN, NULL, KEYBOARD_ICO, [this]() {
    display_obj.clearScreen();
    this->drawStatusBar();
    wifi_scan_obj.StartScan(BT_ATTACK_SWIFTPAIR_SPAM, TFT_CYAN);
  });
  this->addNodes(&bluetoothAttackMenu, "Samsung BLE Spam", TFTRED, NULL, GENERAL_APPS, [this]() {
    display_obj.clearScreen();
    this->drawStatusBar();
    wifi_scan_obj.StartScan(BT_ATTACK_SAMSUNG_SPAM, TFT_RED);
  });
  this->addNodes(&bluetoothAttackMenu, "Google BLE Spam", TFTPURPLE, NULL, LANGUAGE, [this]() {
    display_obj.clearScreen();
    this->drawStatusBar();
    wifi_scan_obj.StartScan(BT_ATTACK_GOOGLE_SPAM, TFT_PURPLE);
  });
  this->addNodes(&bluetoothAttackMenu, "Flipper BLE Spam", TFTORANGE, NULL, FLIPPER, [this]() {
    display_obj.clearScreen();
    this->drawStatusBar();
    wifi_scan_obj.StartScan(BT_ATTACK_FLIPPER_SPAM, TFT_ORANGE);
  });
  this->addNodes(&bluetoothAttackMenu, "BLE Spam All", TFTMAGENTA, NULL, DEAUTH_SNIFF, [this]() {
    display_obj.clearScreen();
    this->drawStatusBar();
    wifi_scan_obj.StartScan(BT_ATTACK_SPAM_ALL, TFT_MAGENTA);
  });

  #ifdef HAS_ILI9341
    this->addNodes(&bluetoothAttackMenu, "Spoof Airtag", TFTWHITE, NULL, ATTACKS, [this](){
      display_obj.clearScreen();
      wifi_scan_obj.currentScanMode = LV_ADD_SSID;
      wifi_scan_obj.StartScan(LV_ADD_SSID, TFT_WHITE);
      addAPGFX("Airtag");
    });
  #endif

  #ifndef HAS_ILI9341
    #ifdef HAS_BT
    // Select Airtag on Mini
      this->addNodes(&bluetoothAttackMenu, "Spoof Airtag", TFTWHITE, NULL, ATTACKS, [this](){
          // Clear nodes and add back button
          airtagMenu.list->clear();
          this->addNodes(&airtagMenu, text09, TFT_LIGHTGREY, NULL, 0, [this]() {
          this->changeMenu(airtagMenu.parentMenu);
        });

        // Add buttons for all airtags
        // Find out how big our menu is going to be
        int menu_limit;
        if (airtags->size() <= BUTTON_ARRAY_LEN)
          menu_limit = airtags->size();
        else
          menu_limit = BUTTON_ARRAY_LEN;

        // Create the menu nodes for all of the list items
        for (int i = 0; i < menu_limit; i++) {
          this->addNodes(&airtagMenu, airtags->get(i).mac, TFTWHITE, NULL, BLUETOOTH, [this, i](){
            AirTag new_at = airtags->get(i);
            new_at.selected = true;

            airtags->set(i, new_at);

            // Set all other airtags to "Not Selected"
            for (int x = 0; x < airtags->size(); x++) {
              if (x != i) {
                AirTag new_atx = airtags->get(x);
                new_atx.selected = false;
                airtags->set(x, new_atx);
              }
            }

            // Start the spoof
            display_obj.clearScreen();
            this->drawStatusBar();
            wifi_scan_obj.StartScan(BT_SPOOF_AIRTAG, TFT_WHITE);

          });
        }
        this->changeMenu(&airtagMenu);
      });

      airtagMenu.parentMenu = &bluetoothAttackMenu;
      this->addNodes(&airtagMenu, text09, TFTLIGHTGREY, NULL, 0, [this]() {
        this->changeMenu(airtagMenu.parentMenu);
      });
    #endif

  #endif

  // Device menu
  deviceMenu.parentMenu = &mainMenu;
  this->addNodes(&deviceMenu, text09, TFTLIGHTGREY, NULL, 0, [this]() {
    this->changeMenu(deviceMenu.parentMenu);
  });
  this->addNodes(&deviceMenu, text_table1[15], TFTORANGE, NULL, UPDATE, [this]() {
    wifi_scan_obj.currentScanMode = OTA_UPDATE;
    this->changeMenu(&whichUpdateMenu);
  });

  this->addNodes(&deviceMenu, "Save/Load Files", TFTCYAN, NULL, SD_UPDATE, [this]() {
    this->changeMenu(&saveFileMenu);
  });

  this->addNodes(&deviceMenu, text_table1[16], TFTGREEN, NULL, LANGUAGE, [this]() {

    wifi_scan_obj.currentScanMode = SHOW_INFO;
    this->changeMenu(&languageMenu);   
  });
  this->addNodes(&deviceMenu, text_table1[17], TFTWHITE, NULL, DEVICE_INFO, [this]() {
    wifi_scan_obj.currentScanMode = SHOW_INFO;
    this->changeMenu(&infoMenu);
    wifi_scan_obj.RunInfo();
  });
  this->addNodes(&deviceMenu, text08, TFTNAVY, NULL, KEYBOARD_ICO, [this]() {
    this->changeMenu(&settingsMenu);
  });

  #ifdef HAS_SD
    if (sd_obj.supported) {
      this->addNodes(&deviceMenu, "Delete SD Files", TFTCYAN, NULL, SD_UPDATE, [this]() {
        #ifndef HAS_ILI9341
          #ifdef HAS_BUTTONS
            this->changeMenu(&sdDeleteMenu);
            #if !(defined(MARAUDER_V6) || defined(MARAUDER_V6_1) || defined(MARAUDER_CYD_MICRO))

              bool deleting = true;

              display_obj.tft.setTextWrap(false);
              display_obj.tft.setCursor(0, SCREEN_HEIGHT / 3);
              display_obj.tft.setTextColor(TFT_CYAN, TFT_BLACK);
              display_obj.tft.println("Loading...");

              while (deleting) {
                // Build list of files
                sd_obj.sd_files->clear();
                delete sd_obj.sd_files;

                sd_obj.sd_files = new LinkedList<String>();

                sd_obj.sd_files->add("Back");

                sd_obj.listDirToLinkedList(sd_obj.sd_files);

                int sd_file_index = 0;

                this->sdDeleteMenu.list->set(0, MenuNode{sd_obj.sd_files->get(sd_file_index), false, TFTCYAN, 0, NULL, true, NULL});
                this->buildButtons(&sdDeleteMenu);
                this->displayCurrentMenu();

                // Start button loop
                while(true) {
                  #if !defined(MARAUDER_M5STICKC) || defined(MARAUDER_M5STICKCP2)
                    #if (U_BTN >= 0 || defined(MARAUDER_CARDPUTER))
                    #if (U_BTN >= 0)
                      if (u_btn.justPressed()){
                    #elif defined(MARAUDER_CARDPUTER)
                      if (this->isKeyPressed(';')){
                    #endif
                      if (sd_file_index > 0)
                        sd_file_index--;
                      else
                        sd_file_index = sd_obj.sd_files->size() - 1;

                      this->sdDeleteMenu.list->set(0, MenuNode{sd_obj.sd_files->get(sd_file_index), false, TFTCYAN, 0, NULL, true, NULL});
                      this->buildButtons(&sdDeleteMenu);
                      this->displayCurrentMenu();
                    }
                    #endif
                  #endif
                  #if (D_BTN >= 0 || defined(MARAUDER_CARDPUTER))
                  #if (D_BTN >= 0)
                  if (d_btn.justPressed()){
                  #elif defined(MARAUDER_CARDPUTER)
                  if (this->isKeyPressed('.')){
                  #endif
                    if (sd_file_index < sd_obj.sd_files->size() - 1)
                      sd_file_index++;
                    else
                      sd_file_index = 0;
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
