lucsch/ESP32Marauder/esp32_marauder/Assets.h

#pragma once

#ifndef Assets_h
#define Assets_h

#include "configs.h"

//#define jquery_min_js_v3_2_1_gz_len 30178

PROGMEM static String espressif_macs[] = {
  "fc:f5:c4"};

PROGMEM static const unsigned char menu_icons[][66] = {
    {0xFF, 0xFF, 0x3F, 0xFF, 0xFF, 0x3F, 0xFF, 0xFF, 0x37, 0xFF, 0xFF, 0x3A, // Attack: 0
    0xFF, 0xFF, 0x39, 0xFF, 0xBF, 0x3C, 0xFF, 0x7F, 0x3E, 0xFF, 0x2F, 0x3F, 
    0xFF, 0x9F, 0x3F, 0xFF, 0xCB, 0x3F, 0xFF, 0xE7, 0x3F, 0xCF, 0xF2, 0x3F, 
    0xDF, 0xF9, 0x3F, 0xBF, 0xFC, 0x3F, 0x3F, 0xFF, 0x3F, 0x7F, 0xFE, 0x3F, 
    0xDF, 0xF9, 0x3F, 0xCF, 0xFB, 0x3F, 0xE7, 0xFF, 0x3F, 0xF3, 0xFF, 0x3F, 
    0xFF, 0xFF, 0x3F, 0xFF, 0xFF, 0x3F},
    {0xBF, 0xDD, 0x3E, 0xDF, 0xBE, 0x3D, 0x5F, 0x6B, 0x3D, 0x5F, 0x5D, 0x3D, // Beacon sniff: 1
    0x5F, 0x55, 0x3D, 0xFF, 0xF7, 0x3F, 0xFF, 0xF7, 0x3F, 0xFF, 0xEB, 0x3F, 
    0xFF, 0xEB, 0x3F, 0xFF, 0xEB, 0x3F, 0xFF, 0xDD, 0x3F, 0xFF, 0xD5, 0x3F, 
    0xFF, 0xC9, 0x3F, 0xFF, 0xDD, 0x3F, 0xFF, 0xC9, 0x3F, 0xFF, 0xB6, 0x3F, 
    0xFF, 0xAA, 0x3F, 0xFF, 0x9C, 0x3F, 0xFF, 0xAA, 0x3F, 0x7F, 0x77, 0x3F, 
    0x7F, 0x49, 0x3F, 0x7F, 0x3E, 0x3F},
    {0xFF, 0xFF, 0x3F, 0xFF, 0xFF, 0x3F, 0xFF, 0xFF, 0x3F, 0xFF, 0xFB, 0x3F, // Bluetooth: 2
    0xFF, 0xF3, 0x3F, 0xFF, 0xEB, 0x3F, 0xFF, 0xDB, 0x3F, 0x7F, 0xBB, 0x3F, 
    0xFF, 0xDA, 0x3F, 0xFF, 0xE9, 0x3F, 0xFF, 0xF3, 0x3F, 0xFF, 0xF3, 0x3F, 
    0xFF, 0xE9, 0x3F, 0xFF, 0xDA, 0x3F, 0x7F, 0xBB, 0x3F, 0xFF, 0xDB, 0x3F, 
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
    0x38, 0x39, 0x3A, 0x43, 0x44, 0x45, 0x46, 0x47, 0x48, 0x49, 0x4A, 0x53, 0x54, 0x55, 0x56, 0x57, 
    0x58, 0x59, 0x5A, 0x63, 0x64, 0x65, 0x66, 0x67, 0x68, 0x69, 0x6A, 0x73, 0x74, 0x75, 0x76, 0x77, 
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
    
#endif
*/

#endif
